dekuNukem/duckyPad/pcb/V2/duckypad v2 dimensions.png

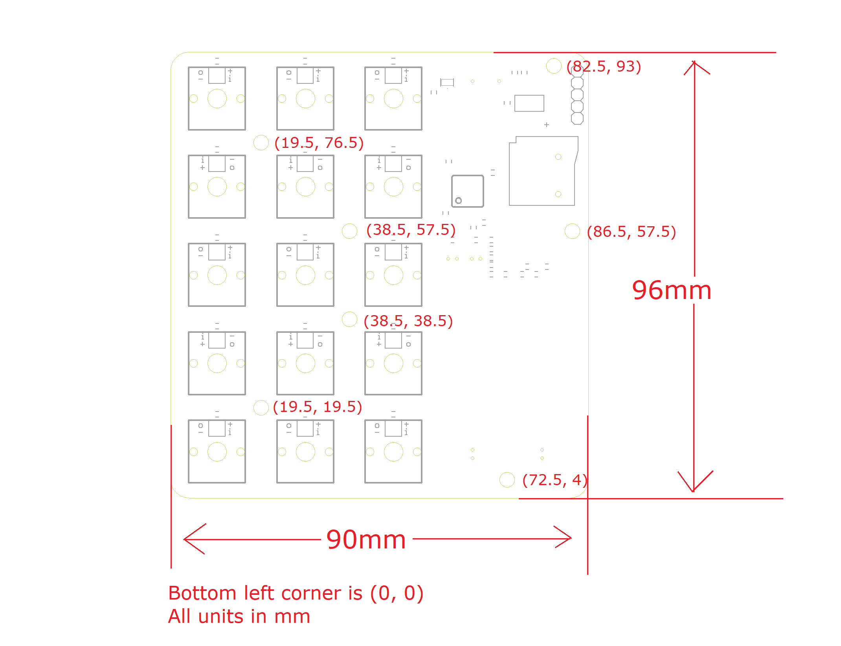
pcb/V2/duckypad v2 dimensions.png
