dekuNukem/duckyPad/resources/Keyboard scancodes Japanese keyboards_files/imb5576-2.jpg

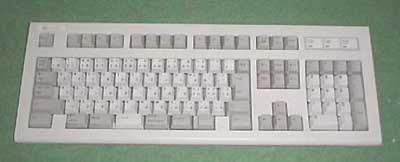
resources/Keyboard scancodes Japanese keyboards_files/imb5576-2.jpg
