dekuNukem/duckyPad/resources/Keyboard scancodes Japanese keyboards_files/jp106-with-scancodes.jpg

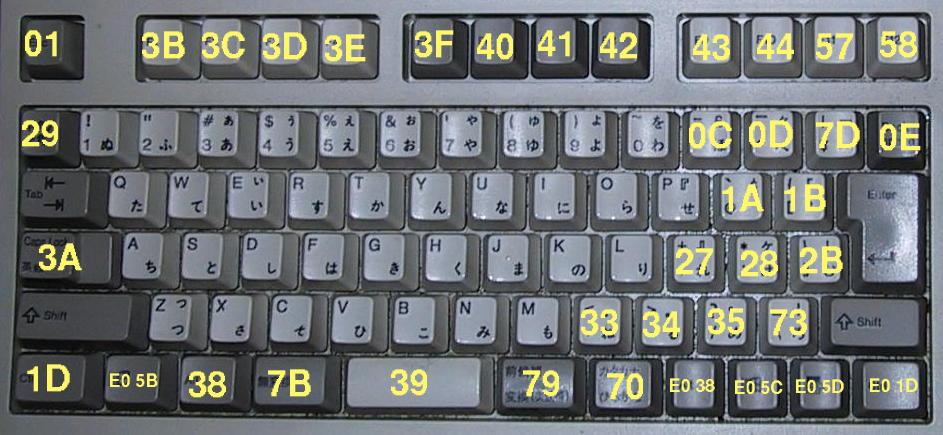
resources/Keyboard scancodes Japanese keyboards_files/jp106-with-scancodes.jpg
