dekuNukem/duckyPad/resources/Keyboard scancodes Japanese keyboards_files/jp106.jpg

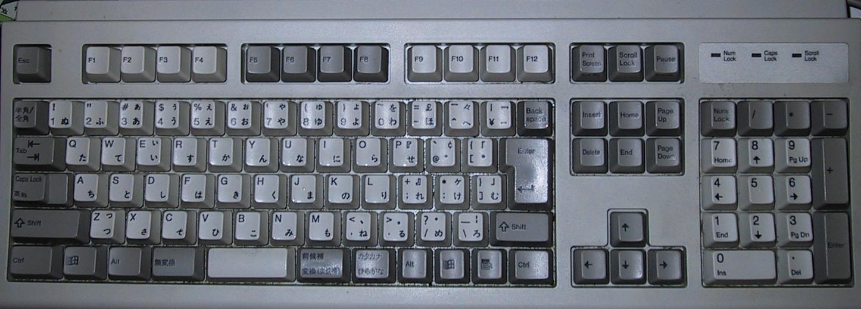
resources/Keyboard scancodes Japanese keyboards_files/jp106.jpg
