dekuNukem/duckyPad/resources/pics/buttons.jpg

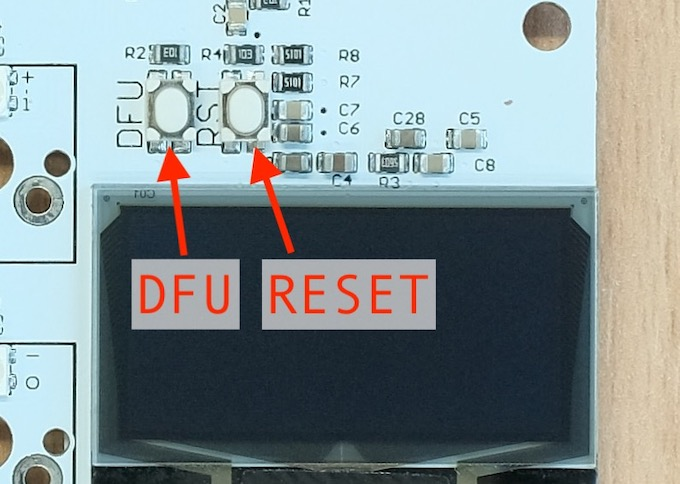
resources/pics/buttons.jpg
