dekuNukem/duckyPad/resources/pics/cable.jpg

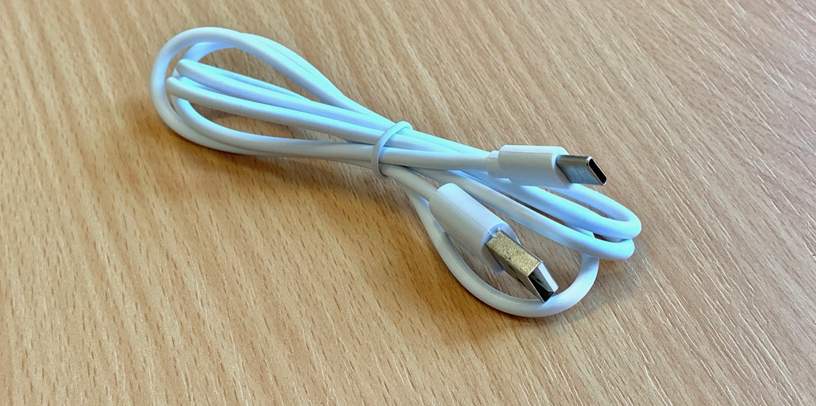
resources/pics/cable.jpg
