dekuNukem/duckyPad/resources/pics/dimensions.png

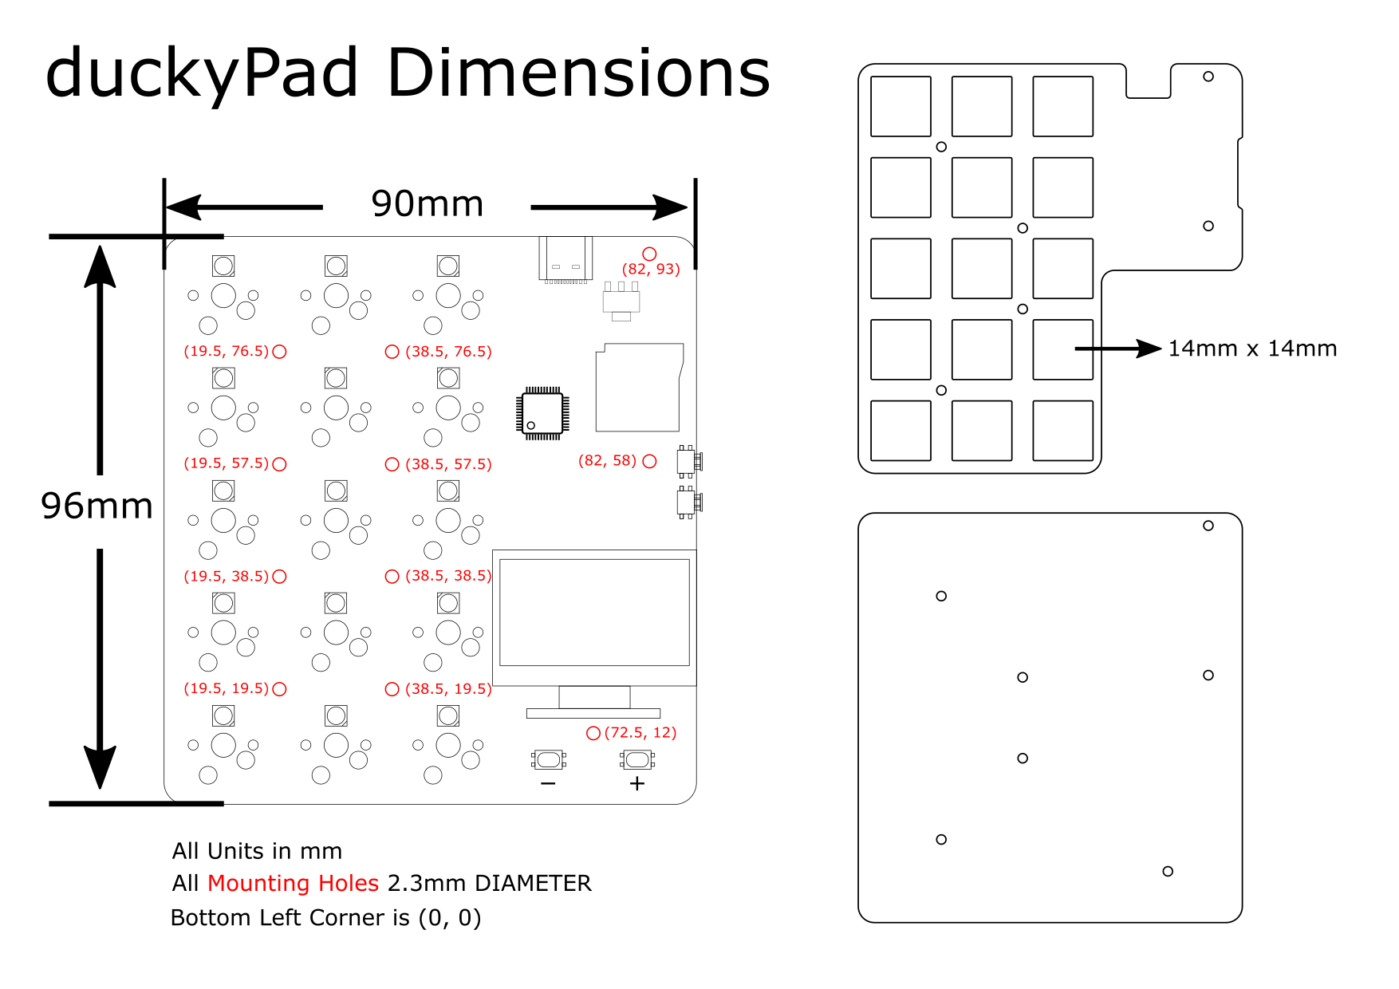
resources/pics/dimensions.png
