dekuNukem/duckyPad/resources/pics/hello.gif

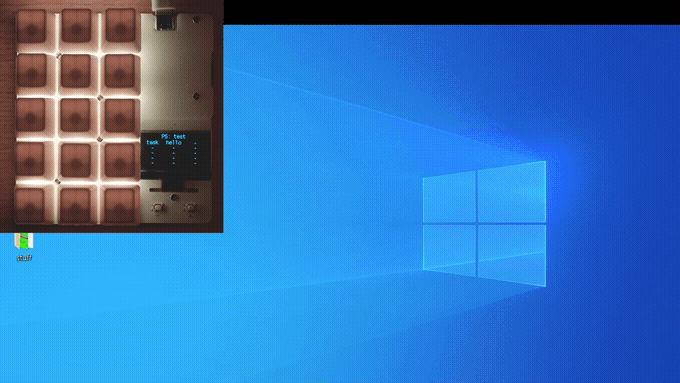
resources/pics/hello.gif
