dekuNukem/duckyPad/resources/pics/input_mon.png

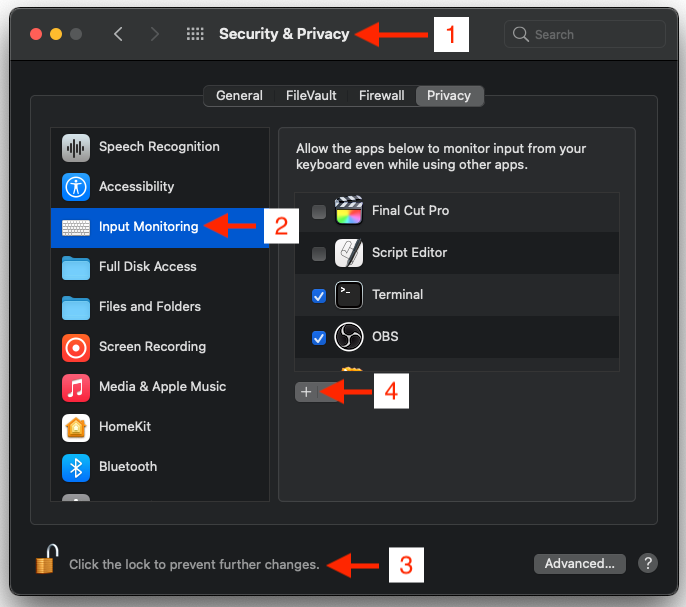
resources/pics/input_mon.png
