dekuNukem/duckyPad/resources/pics/keymaps/dead.png

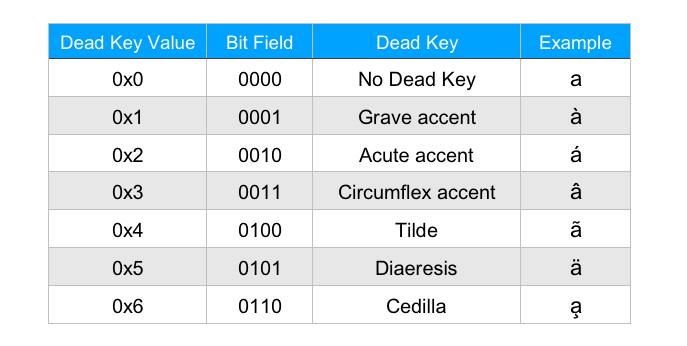
resources/pics/keymaps/dead.png
