dekuNukem/duckyPad/resources/pics/right.png

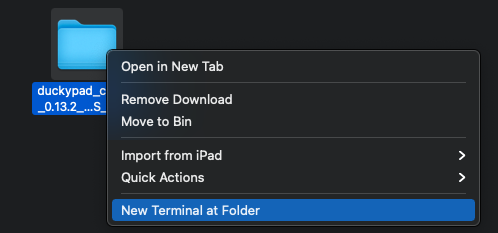
resources/pics/right.png
