dekuNukem/duckyPad/resources/pics/screen_rec.png

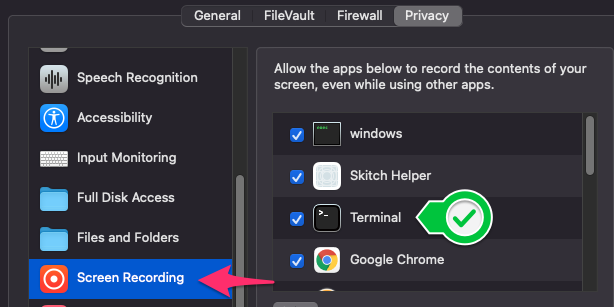
resources/pics/screen_rec.png
