dekuNukem/duckyPad/resources/pics/sd.jpg

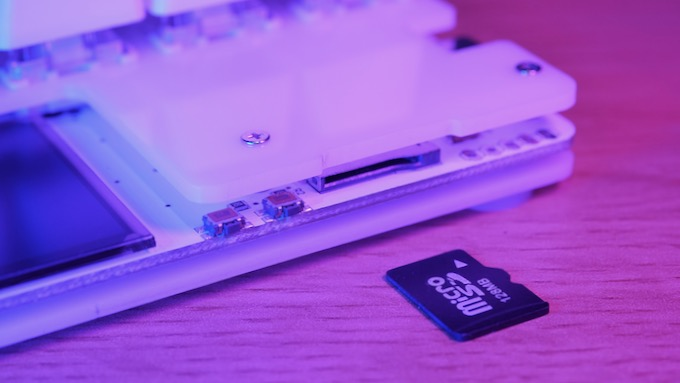
resources/pics/sd.jpg
