dekuNukem/duckyPad/resources/pics/sd_card.PNG

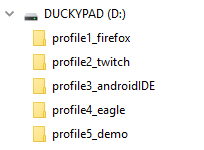
resources/pics/sd_card.PNG
