dekuNukem/duckyPad/resources/pics/sd_reader.jpg

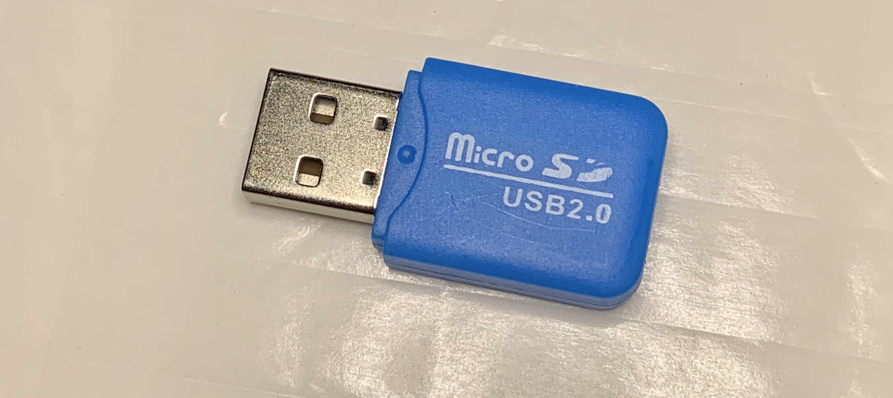
resources/pics/sd_reader.jpg
