dekuNukem/duckyPad/resources/pics/select_term.png

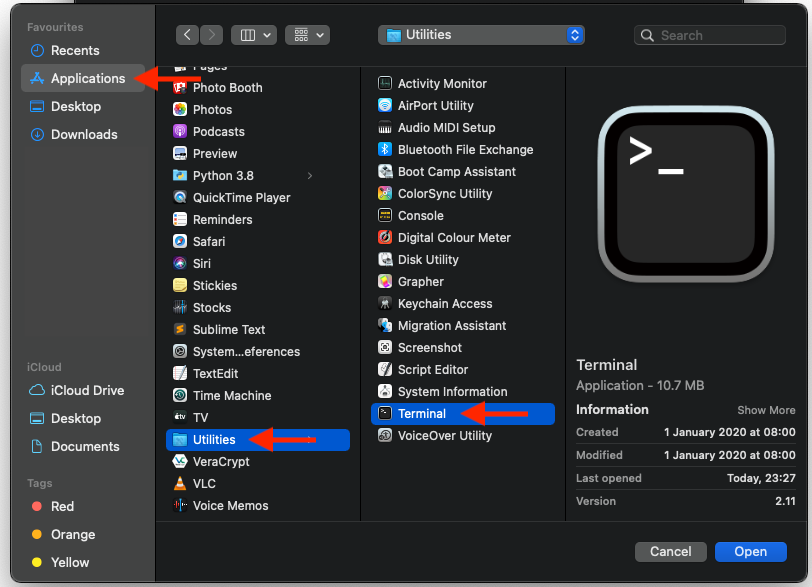
resources/pics/select_term.png
