dekuNukem/duckyPad/resources/pics/start.png

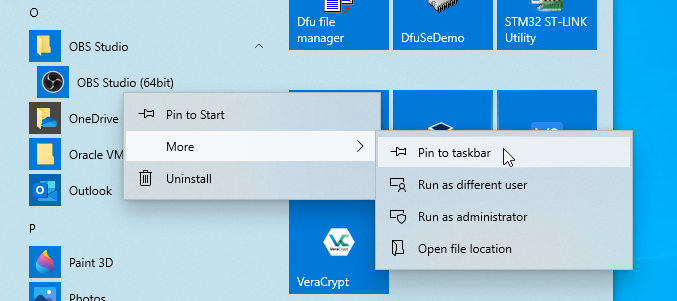
resources/pics/start.png
