dekuNukem/duckyPad/resources/pics/switch.jpg

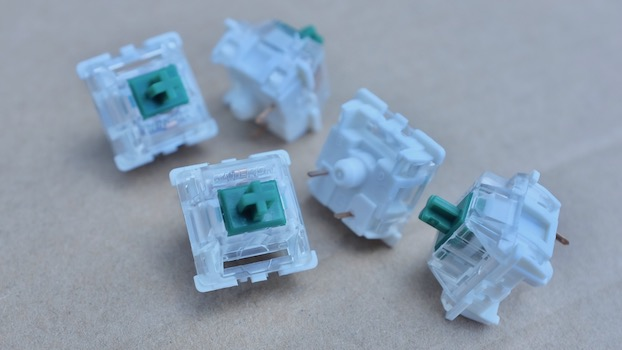
resources/pics/switch.jpg
