dekuNukem/duckyPad/resources/pics/t1.png

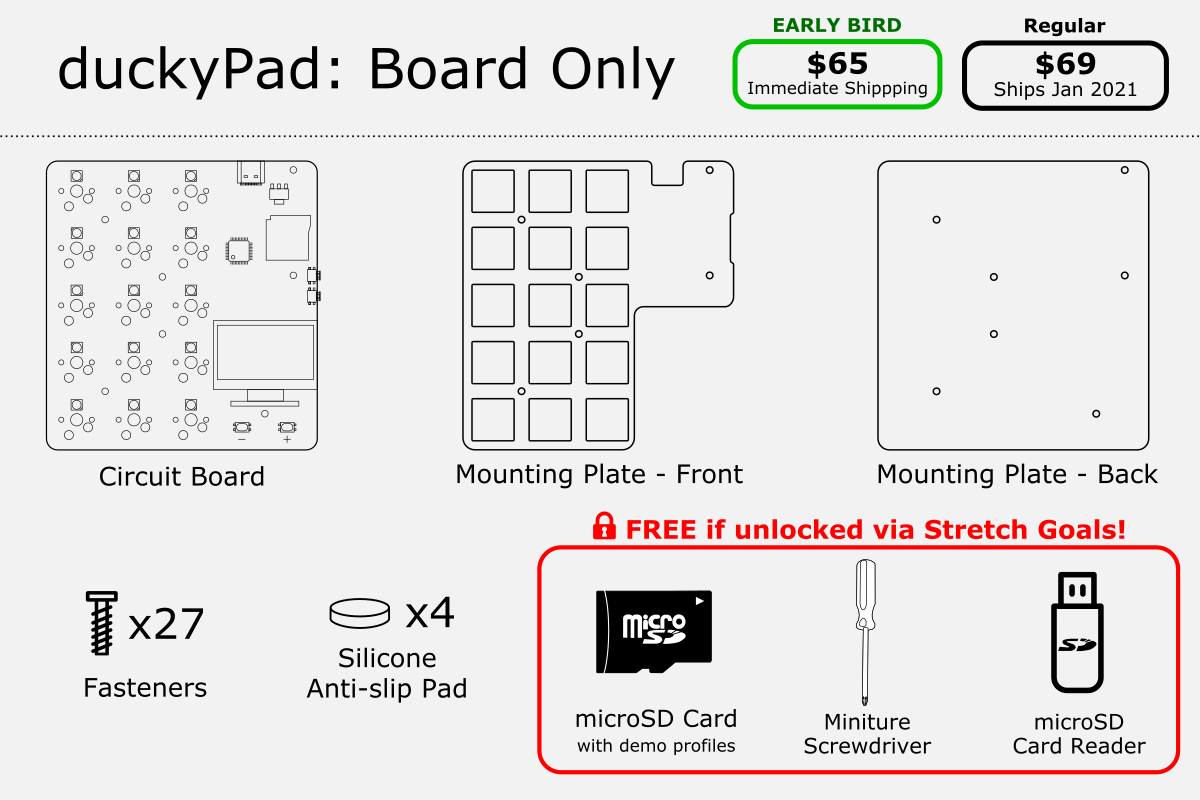
resources/pics/t1.png
