dekuNukem/duckyPad/resources/pics/t2.png

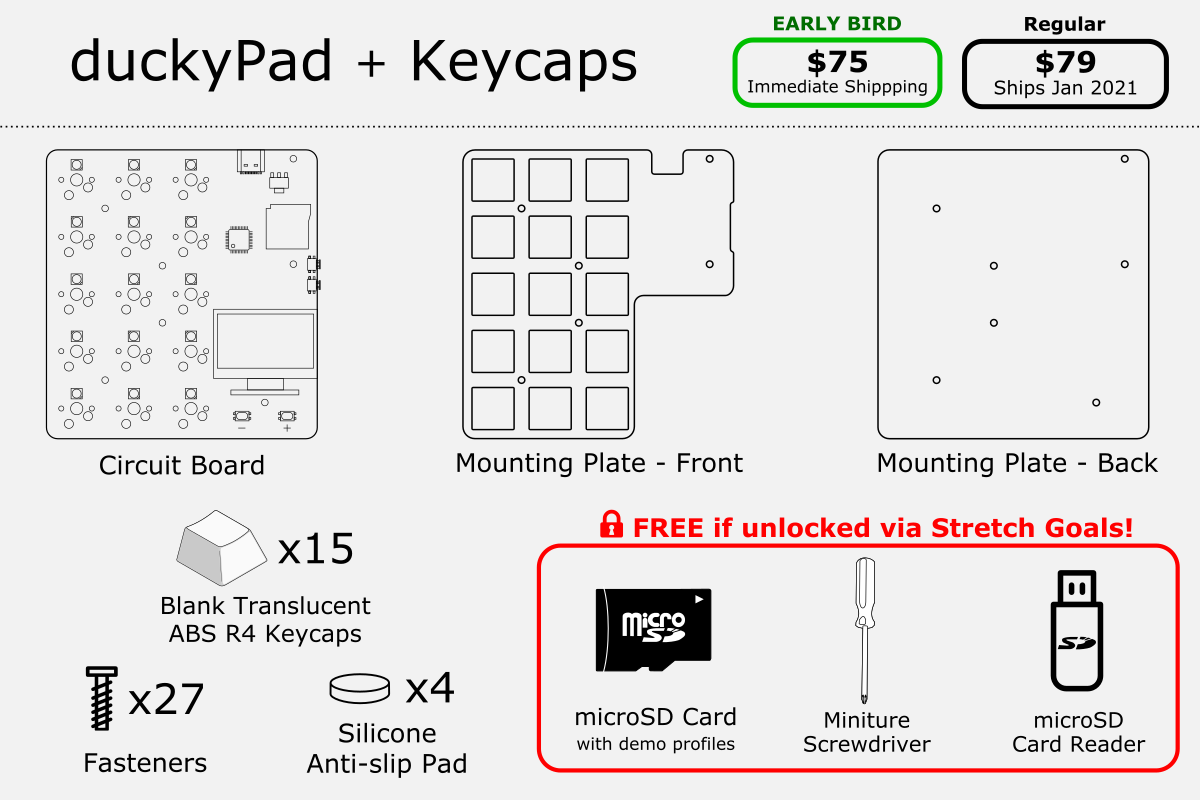
resources/pics/t2.png
