dekuNukem/duckyPad/resources/pics/t3.png

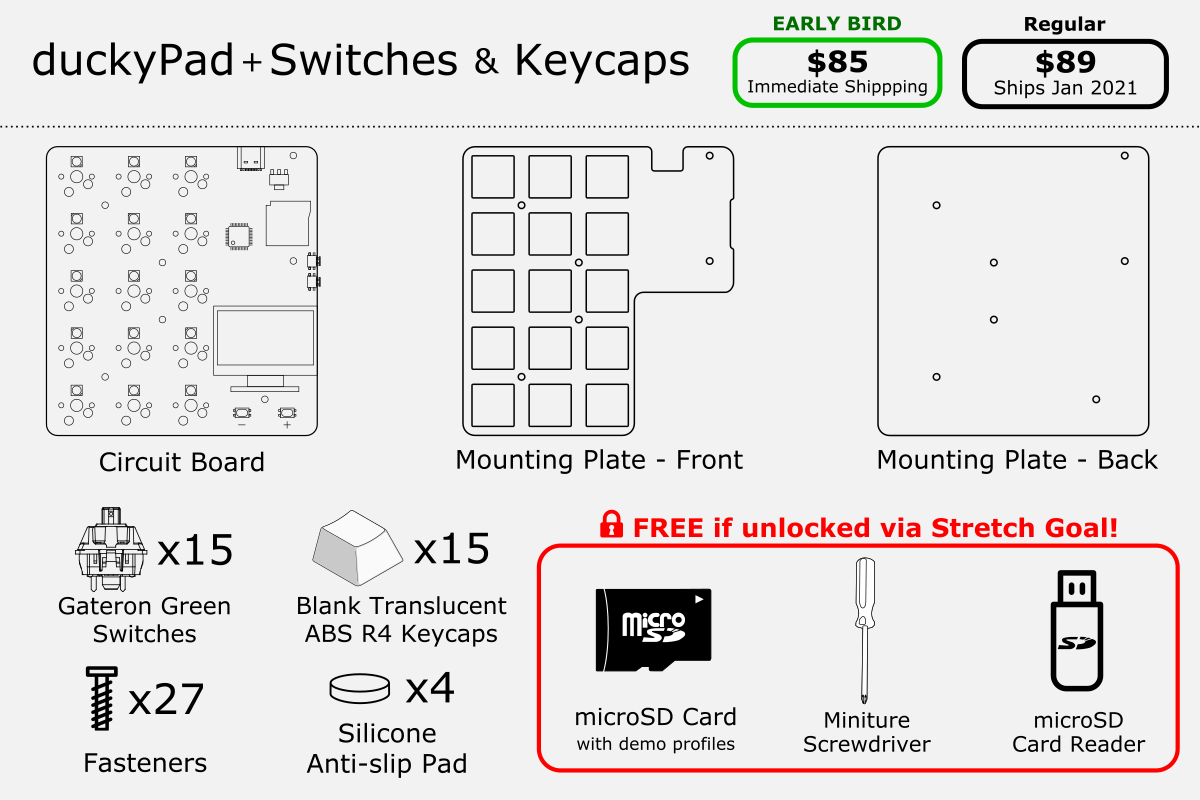
resources/pics/t3.png
