dekuNukem/duckyPad/resources/pics/task.gif

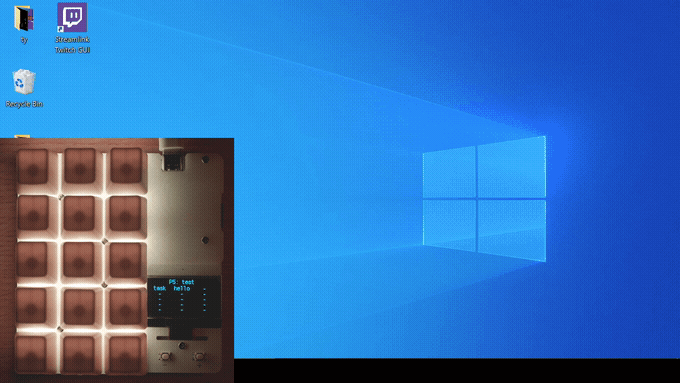
resources/pics/task.gif
