dekuNukem/duckyPad/resources/pics/terminal.png

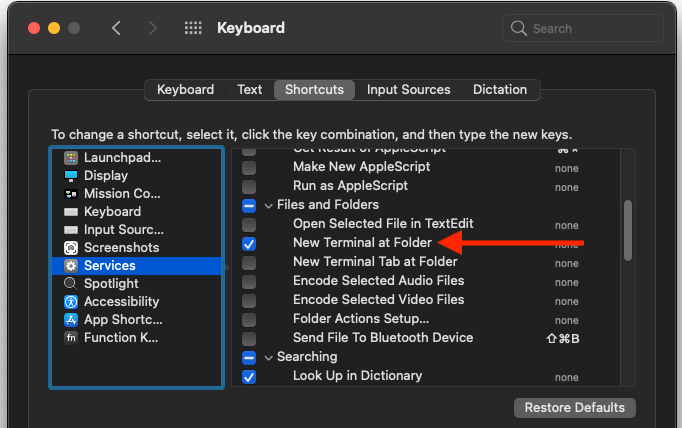
resources/pics/terminal.png
