dekuNukem/duckyPad/resources/pics/tier1.jpg

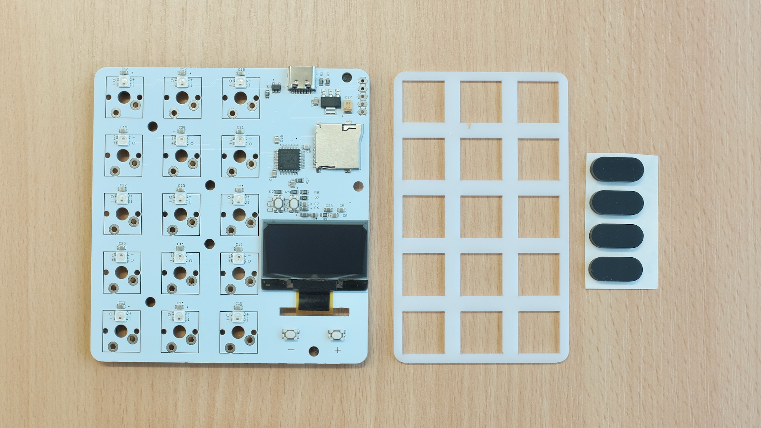
resources/pics/tier1.jpg
