dekuNukem/duckyPad/resources/pics/tier2.jpg

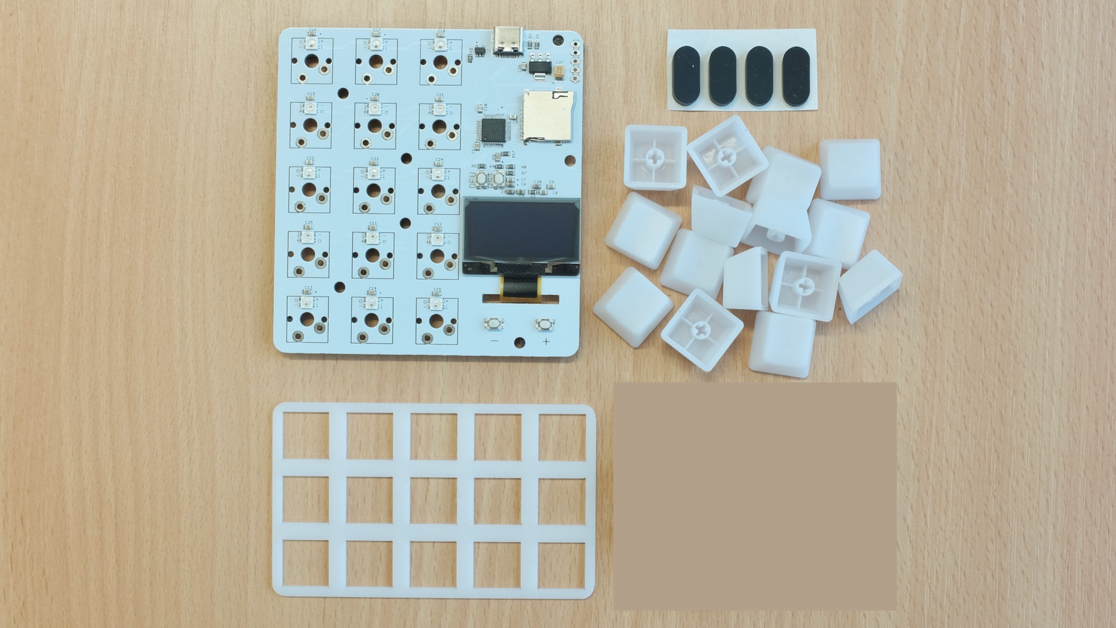
resources/pics/tier2.jpg
