dekuNukem/duckyPad/resources/pics/tier3.jpg

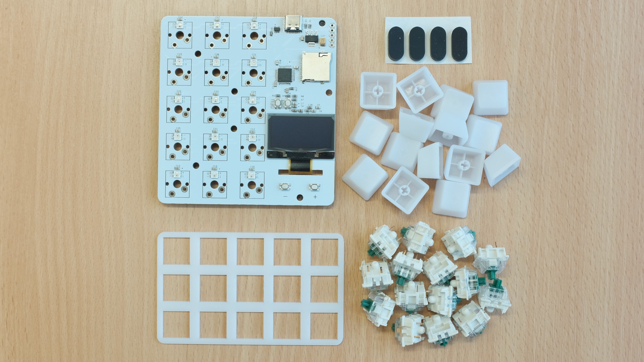
resources/pics/tier3.jpg
