dekuNukem/duckyPad/resources/pics/topdown.jpg

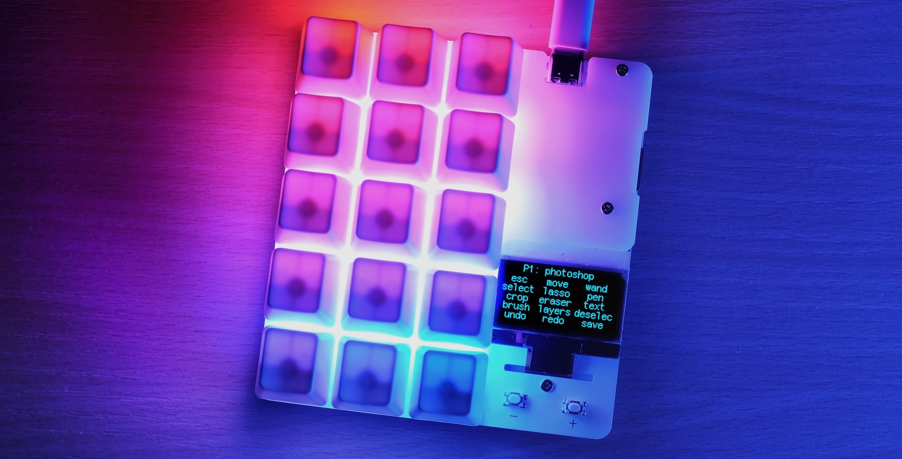
resources/pics/topdown.jpg
