dekuNukem/duckyPad/resources/pics/video.png

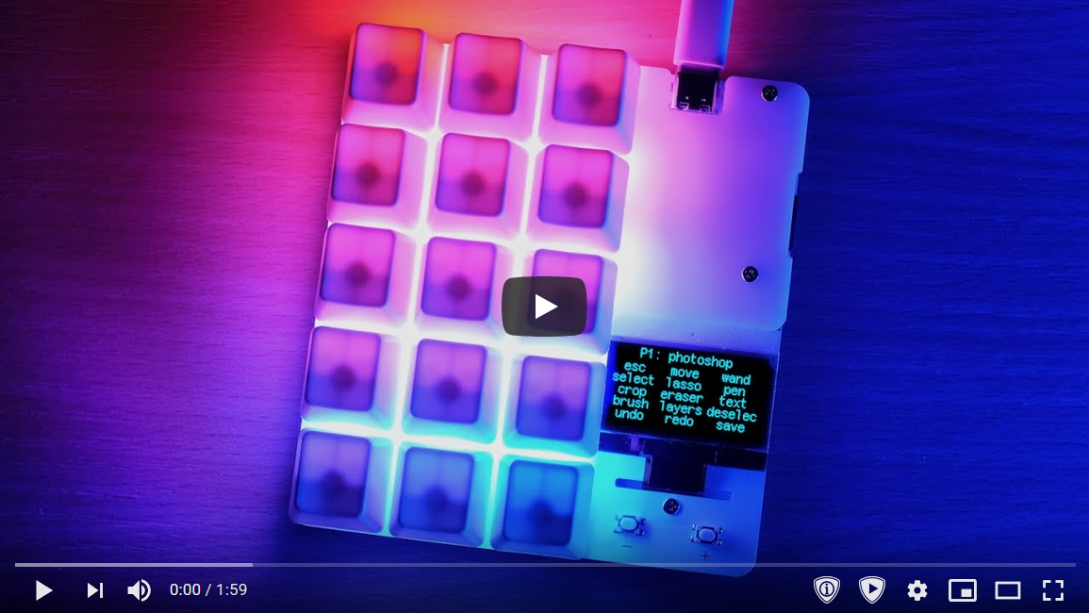
resources/pics/video.png
