dekuNukem/duckyPad/resources/pics/win.png

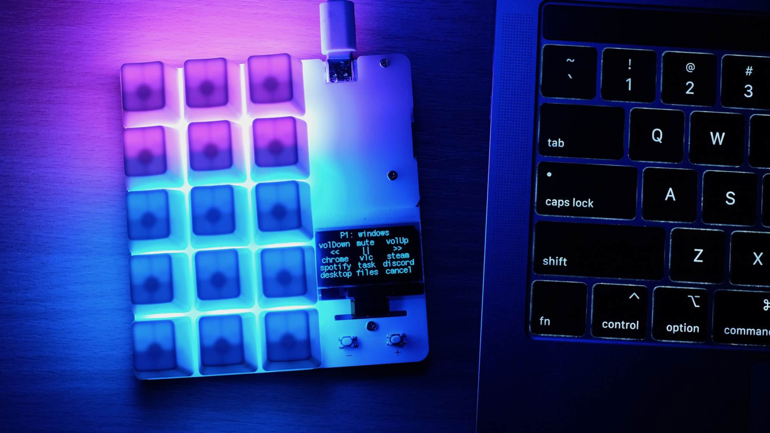
resources/pics/win.png
