dekuNukem/duckyPad/resources/pics/winapps.gif

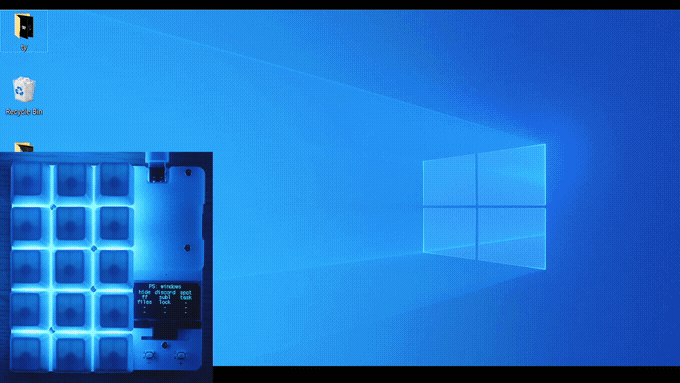
resources/pics/winapps.gif
