dekuNukem/duckyPad/resources/color_tests/image.png

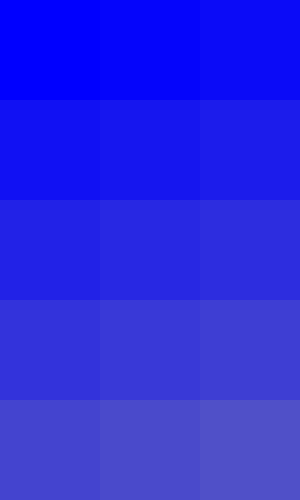
resources/color_tests/image.png
