dekuNukem/duckyPad/resources/SparkFun-Cherry-MX-Switch-Breakout.brd

## EAGLE design resources/SparkFun-Cherry-MX-Switch-Breakout.brd (2019-06-09)

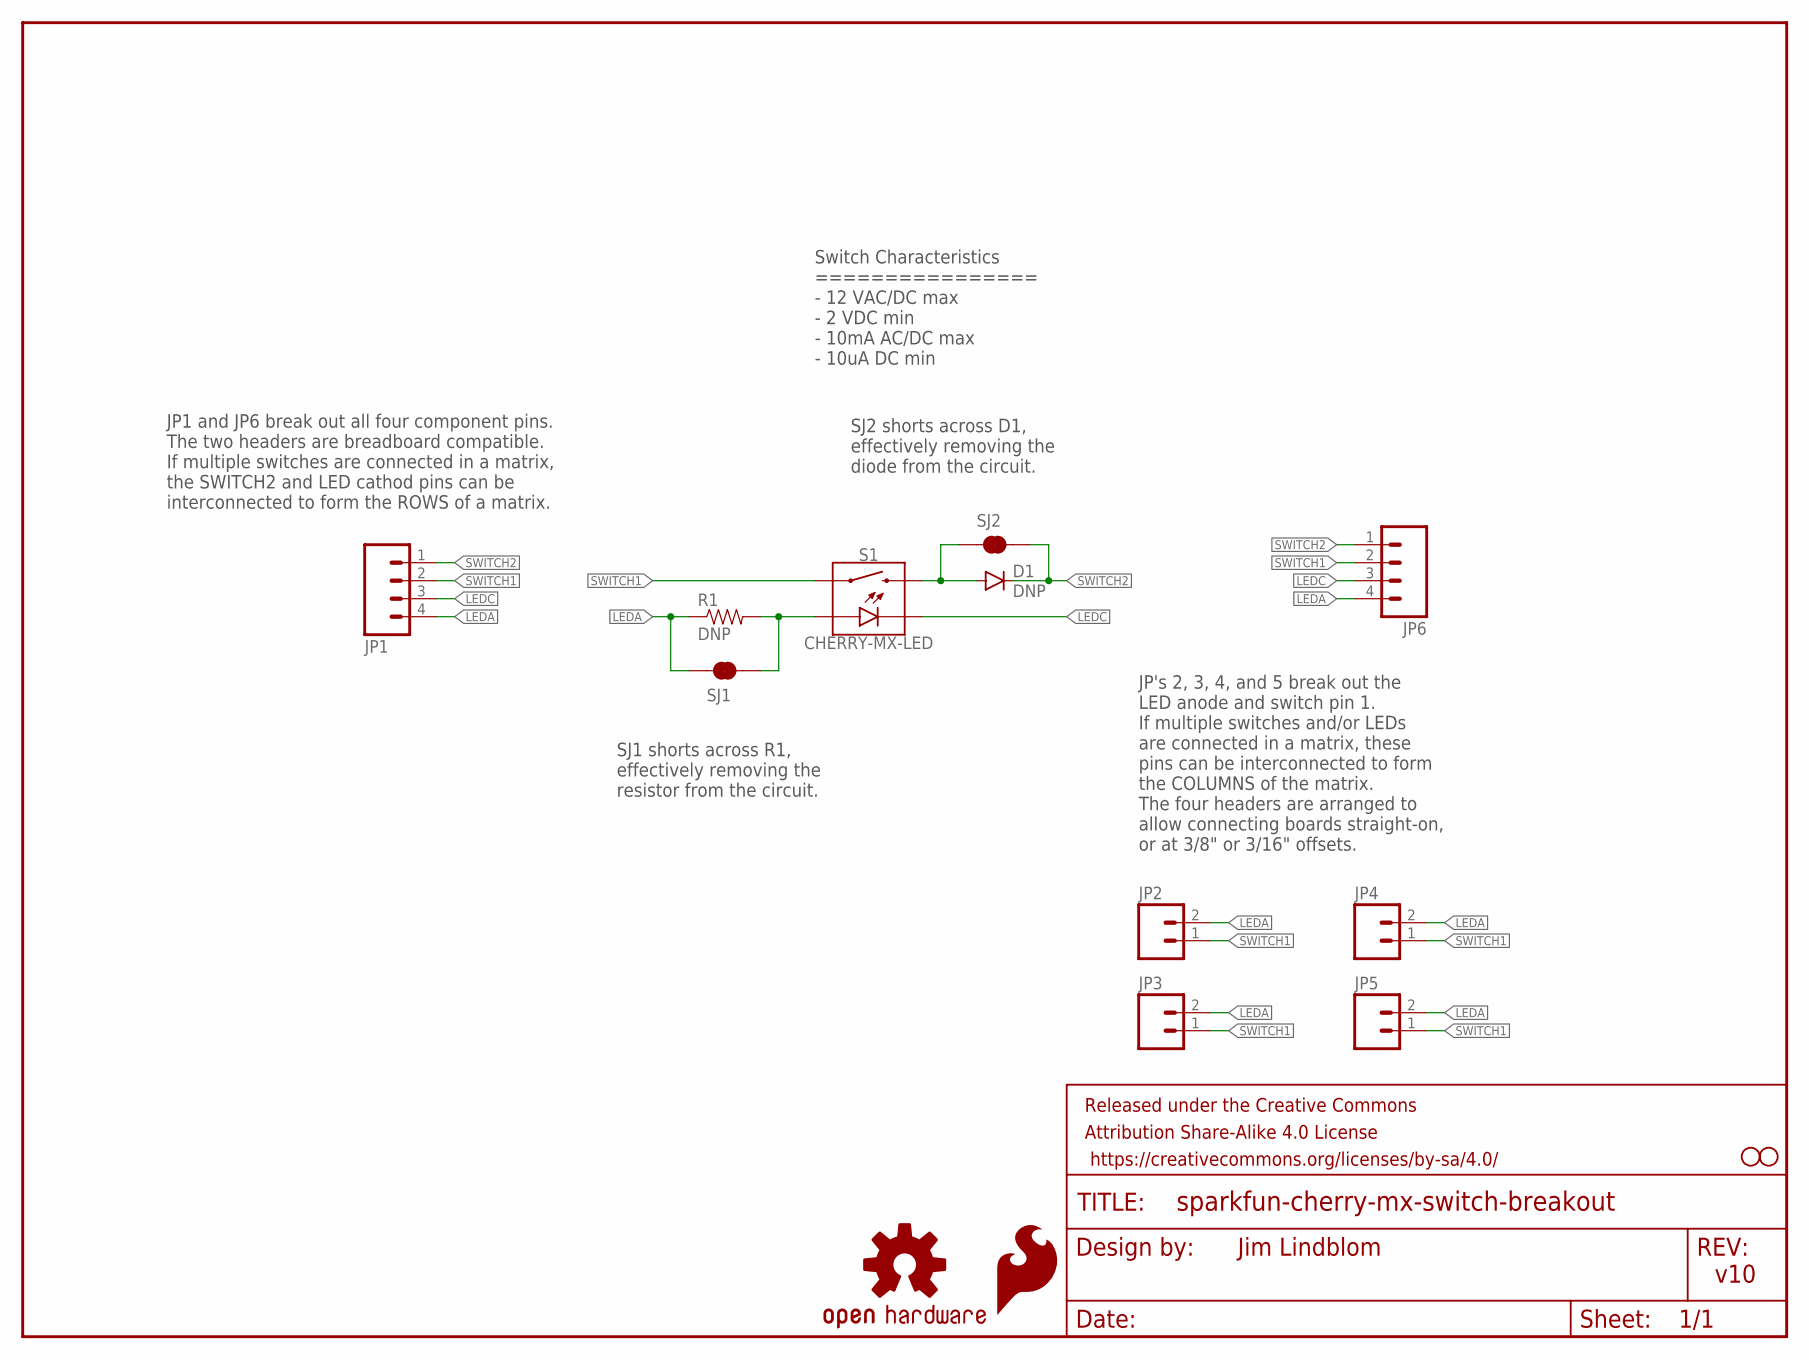
[picture p116: schematic SparkFun-Cherry-MX-Switch-Breakout.sch]

Parts:
D1: DNP; DIODE-PTH-0.1
FRAME1: FRAME-LETTER; CREATIVE_COMMONS
JP1, JP6: M04NO_SILK_ALL_ROUND; 1X04_NO_SILK_ALL_ROUND
JP2, JP3, JP4, JP5: M021X02_NO_SILK; 1X02_NO_SILK
LOGO1: OSHW-LOGOS; OSHW-LOGO-S
LOGO2: SFE_LOGO_FLAME.1_INCH; SFE_LOGO_FLAME_.1
R1: DNP; AXIAL-0.1
S1: CHERRY-MX-LED
SJ1, SJ2: JUMPER-PAD-2-NC_BY_TRACENO_SILK; PAD-JUMPER-2-NC_BY_TRACE_NO_SILK
STANDOFF1, STANDOFF2: STAND-OFF2-56; STAND-OFF-2-56

Connections:
LEDA: JP1.4, JP2.2, JP3.2, JP4.2, JP5.2, JP6.4, R1.P$1 (1), SJ1.1
LEDC: JP1.3, JP6.3, S1.K (C)
unnamed: R1.P$2 (2), S1.A, SJ1.2
unnamed: D1.A, S1.S2, SJ2.1
SWITCH1: JP1.2, JP2.1, JP3.1, JP4.1, JP5.1, JP6.2, S1.S1
SWITCH2: D1.C, JP1.1, JP6.1, SJ2.2

Notes on the sheet:
v10
Jim Lindblom
SJ1 shorts across R1, effectively removing the resistor from the circuit.
SJ2 shorts across D1, effectively removing the diode from the circuit.
JP's 2, 3, 4, and 5 break out the LED anode and switch pin 1. If multiple switches and/or LEDs are connected in a matrix, these pins can be interconnected to form the COLUMNS of the matrix. The four headers are arranged to allow connecting boards straight-on, or at 3/8" or 3/16" offsets.
JP1 and JP6 break out all four component pins. The two headers are breadboard compatible. If multiple switches are connected in a matrix, the SWITCH2 and LED cathod pins can be interconnected to form the ROWS of a matrix.
Switch Characteristics ================ - 12 VAC/DC max - 2 VDC min - 10mA AC/DC max - 10uA DC min

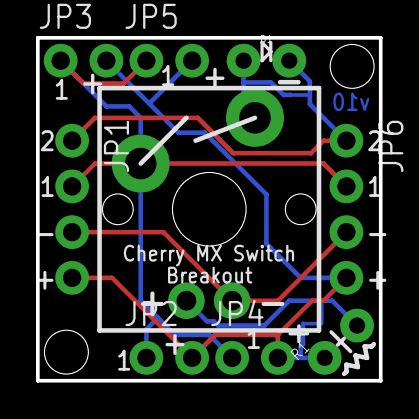
[picture p117: board SparkFun-Cherry-MX-Switch-Breakout.brd from above]

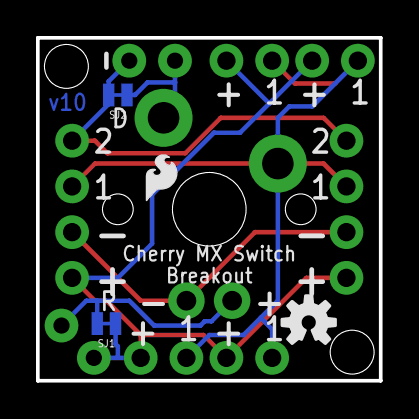
[picture p118: board SparkFun-Cherry-MX-Switch-Breakout.brd from below]

Board: 2 copper layers, 19.1 x 19.1 mm, 16 parts (4 on the bottom side), 6 nets.
