dekuNukem/duckyPad/resources/Adafruit-1.3inch-128x64-Mono-OLED-PCB-master/Adafruit_1.3_128x64_OLED.brd

## EAGLE design resources/Adafruit-1.3inch-128x64-Mono-OLED-PCB-master/Adafruit_1.3_128x64_OLED.brd (2017-08-24)

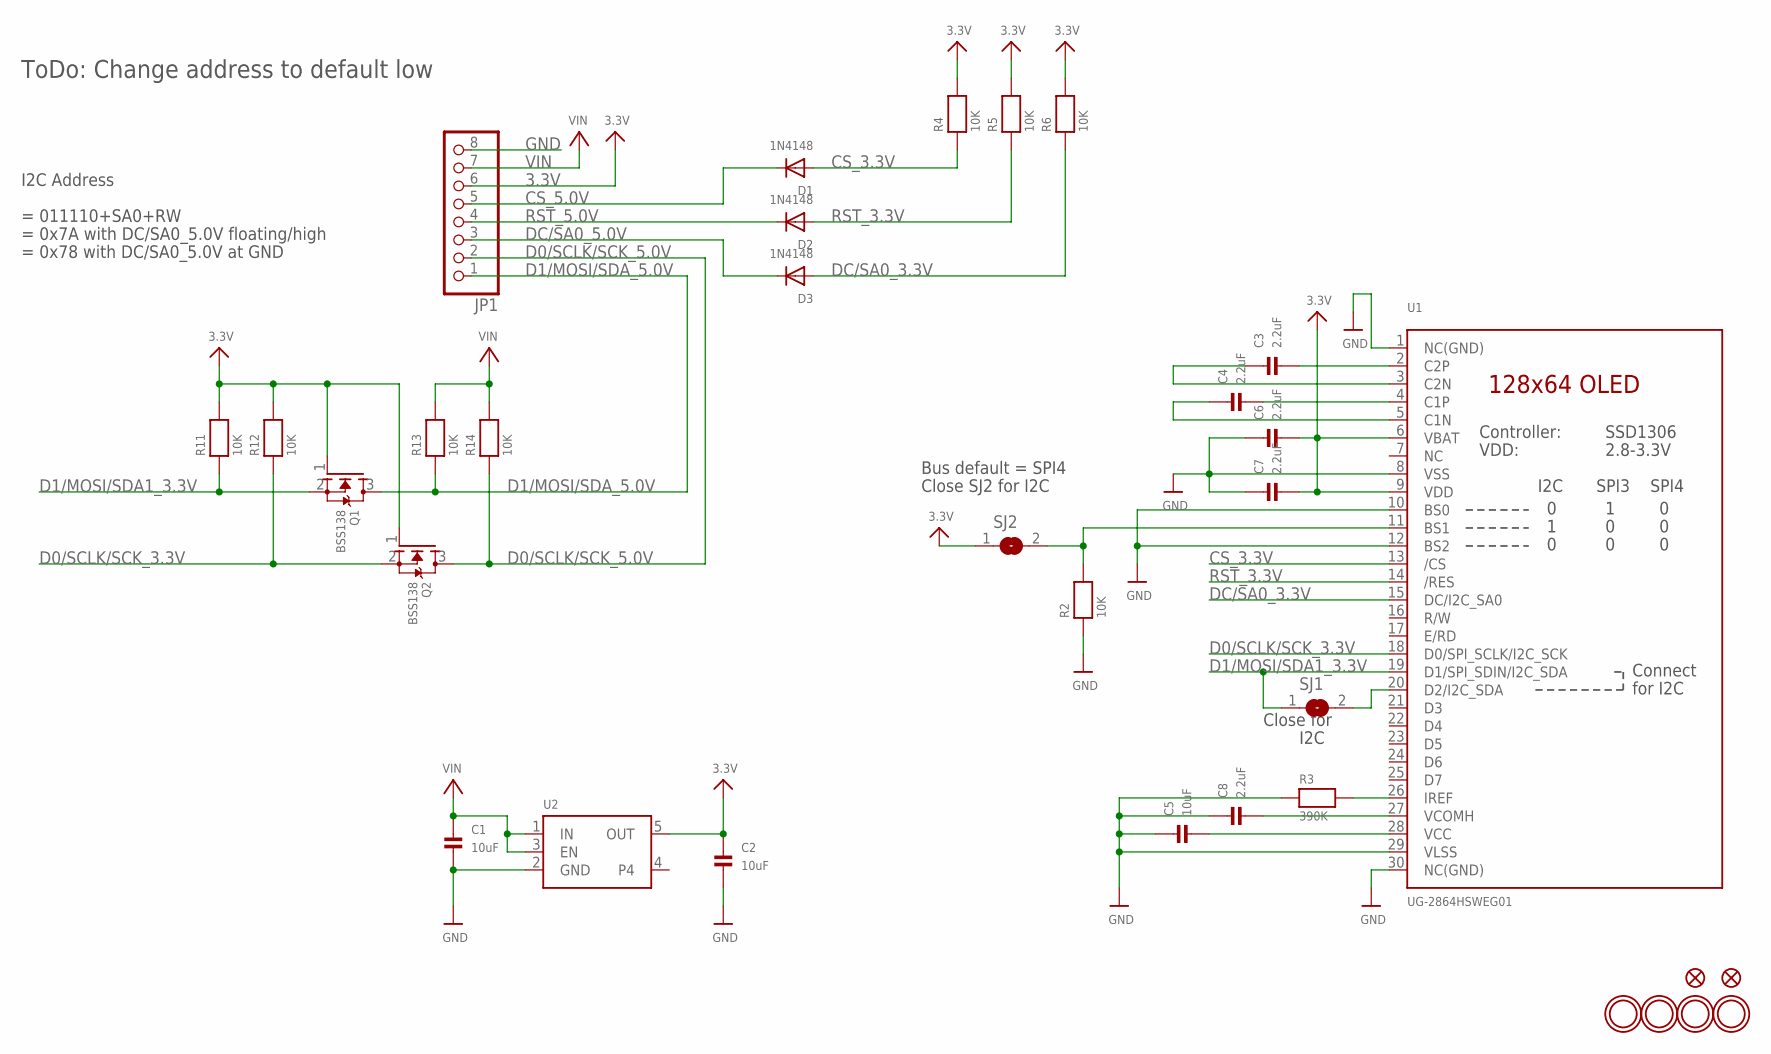
[picture p119: schematic Adafruit_1.3_128x64_OLED.sch]

Parts:
C1, C2, C5: 10uF; 0805
C3, C4, C6, C7, C8: 2.2uF; 0805
D1, D2, D3: 1N4148; SOD-323
FID1, FID2: FIDUCIAL""; FIDUCIAL_1MM
JP1: HEADER-1X870MIL; 1X08_ROUND_70
Q1, Q2: BSS138; SOT23-WIDE
R2, R4, R5, R6, R11, R12, R13, R14: 10K; 0805
R3: 390K; 0805
SJ1, SJ2: SOLDERJUMPERREFLOW_NOPASTE; SOLDERJUMPER_REFLOW_NOPASTE
U1: UG-2864HSWEG01; UG-2864HSWEG01_1.3_WRAPAROUND
U2: VREG_SOT23-5; SOT23-5
U$23, U$24, U$25, U$26: MOUNTINGHOLE2.5; MOUNTINGHOLE_2.5_PLATED

Connections:
3.3V: C2.1, C6.2, C7.2, JP1.6, Q1.1 (G), Q2.1 (G), R4.2, R5.2, R6.2, R11.2, R12.2, SJ2.1, U1.6 (VBAT), U1.9 (VDD), U2.5 (OUT)
CS_3.3V: D1.A, R4.1, U1.13 (/CS)
CS_5.0V: D1.C, JP1.5
D0/SCLK/SCK_3.3V: Q2.2 (S), R12.1, U1.18 (D0/SPI_SCLK/I2C_SCK)
D0/SCLK/SCK_5.0V: JP1.2, Q2.3 (D), R14.1
D1/MOSI/SDA1_3.3V: Q1.2 (S), R11.1, SJ1.1, U1.19 (D1/SPI_SDIN/I2C_SDA)
D1/MOSI/SDA_5.0V: JP1.1, Q1.3 (D), R13.1
DC/SA0_3.3V: D3.A, R6.1, U1.15 (DC/I2C_SA0)
DC/SA0_5.0V: D3.C, JP1.3
GND: C1.2, C2.2, C5.1, C6.1, C7.1, C8.1, JP1.8, R2.1, R3.1, U1.1 (NC(GND)), U1.8 (VSS), U1.10 (BS0), U1.12 (BS2), U1.29 (VLSS), U1.30 (NC(GND)), U2.2 (GND)
unnamed: R2.2, SJ2.2, U1.11 (BS1)
unnamed: SJ1.2, U1.20 (D2/I2C_SDA)
unnamed: R3.2, U1.26 (IREF)
unnamed: C3.2, U1.2 (C2P)
unnamed: C3.1, U1.3 (C2N)
unnamed: C4.2, U1.4 (C1P)
unnamed: C4.1, U1.5 (C1N)
unnamed: C5.2, U1.28 (VCC)
unnamed: C8.2, U1.27 (VCOMH)
RST_3.3V: D2.A, R5.1, U1.14 (/RES)
RST_5.0V: D2.C, JP1.4
VIN: C1.1, JP1.7, R13.2, R14.2, U2.1 (IN), U2.3 (EN)

Notes on the sheet:
Bus default = SPI4
Close SJ2 for I2C
= 011110+SA0+RW
= 0x7A with DC/SA0_5.0V floating/high
= 0x78 with DC/SA0_5.0V at GND
I2C Address
ToDo: Change address to default low
Close for
I2C

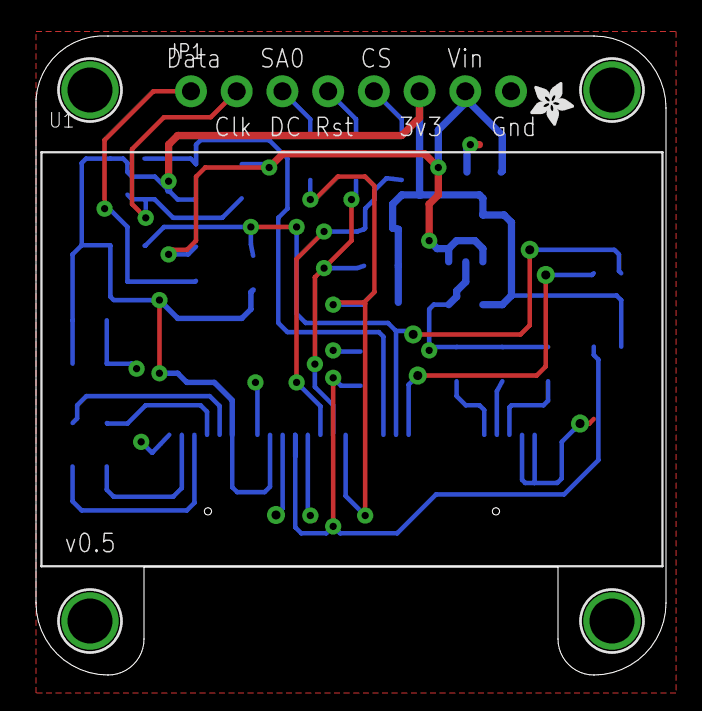
[picture p120: board Adafruit_1.3_128x64_OLED.brd from above]

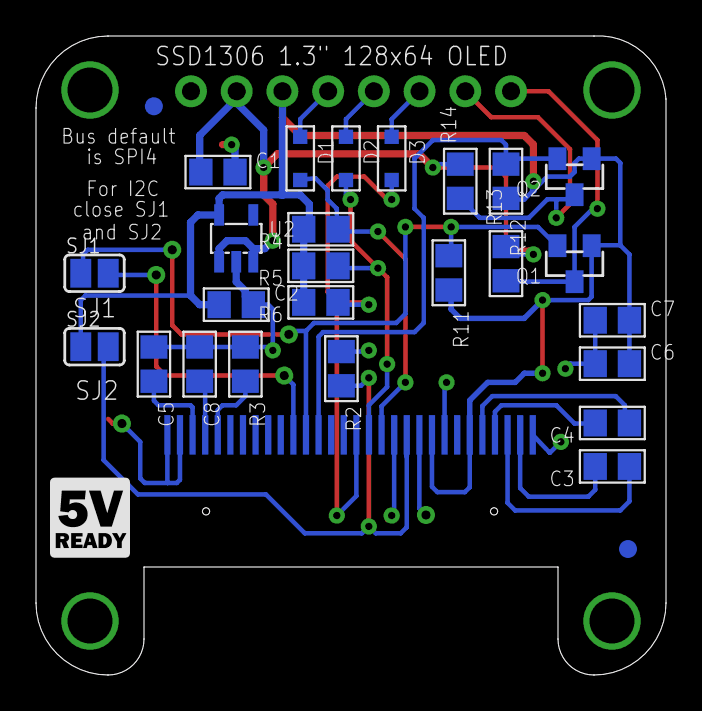
[picture p121: board Adafruit_1.3_128x64_OLED.brd from below]

Board: 2 copper layers, 35.0 x 35.5 mm, 35 parts (28 on the bottom side), 22 nets.

Other parts of the board:
U$27: ADAFRUIT_2.5MM
U$28: LOGIC_5VREADY_5MM
