dekuNukem/duckyPad/firmware/code/Src/main.c

/**
  ******************************************************************************
  * @file           : main.c
  * @brief          : Main program body
  ******************************************************************************
  * This notice applies to any and all portions of this file
  * that are not between comment pairs USER CODE BEGIN and
  * USER CODE END. Other portions of this file, whether 
  * inserted by the user or by software development tools
  * are owned by their respective copyright owners.
  *
  * Copyright (c) 2021 STMicroelectronics International N.V. 
  * All rights reserved.
  *
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
  ******************************************************************************
  */
/* Includes ------------------------------------------------------------------*/
#include "main.h"
#include "stm32f0xx_hal.h"
#include "cmsis_os.h"
#include "fatfs.h"
#include "usb_device.h"

/* USER CODE BEGIN Includes */
#include <stdio.h>
#include <string.h>
#include <stdlib.h>
#include "usbd_customhid.h"
#include "ssd1306.h"
#include "fonts.h"
#include "neopixel.h"
#include "buttons.h"
#include "keyboard.h"
#include "parser.h"
#include "shared.h"
#include "my_tasks.h"
#include "animations.h"

/* USER CODE END Includes */

I2C_HandleTypeDef hi2c1;

IWDG_HandleTypeDef hiwdg;

SPI_HandleTypeDef hspi1;

UART_HandleTypeDef huart1;

osThreadId kb_scanHandle;

/* USER CODE BEGIN PV */

/*
0.20.3 20221031
changed HOLD to EMUK

0.20.4 20221114
add JIS keys

0.21.0 20221117
changed USB HID descriptor so new japanese keys work

0.21.1 20221221
cleaned up animation code
tried out no animation at all, frees up about 1K of ram

0.21.2
massive overhaul to reduce RAM and ROM usage
using hashed lookup for string matching
new keymap select screen
reduced RTOS heap usage
cleaned up animation, much faster
no functional changes
mouse button not implemented yet

0.22.0 20230111
added mouse commands back
ready for public release

0.22.1 20230118
fixed a bug where STRING prints an extra space

1.0.0 20230202
beta release for duckyscript 3

1.1.0 20230214
added banked loading for large dsb files
cleaned up opcode values

1.1.1 20230215
fixed a bug where screen doesnt update when exiting keymap selection screen

1.1.2 20230221
added busy state

1.1.3 20230329
fixing a rand() bug where modulus power of 2 result in repeating patterns

1.1.4 20230409
fixed a SD card timing bug

1.2.0 20230502
ready for public release

1.2.1 20230630
fixed laggy EMUK
fixed EMUK-related n-key rollover bug
fixed pad crashing when changing profiles

1.3.0 20230701
added _TIME_S read-only variable

1.3.1
20231111
increased max profiles to 64
change MAX_PROFILES in parser.h
change BIN_BUF_SIZE in ds3_vm.c if out of space

1.3.2
2024 01 22
fixed backlight brightness saving bug

1.3.3
2024 12 02
Fixed non-responsive mouse scroll bug 

1.3.4
2024 12 18
Fixed dead key behaviour
*/

uint8_t fw_version_major = 1;
uint8_t fw_version_minor = 3;
uint8_t fw_version_patch = 4;
char instruction[] = "For instructions, see";
/* USER CODE END PV */

void SystemClock_Config(void);
static void MX_GPIO_Init(void);
static void MX_USART1_UART_Init(void);
static void MX_SPI1_Init(void);
static void MX_I2C1_Init(void);
static void MX_IWDG_Init(void);
void kb_scan_task(void const * argument);
/* USER CODE BEGIN PFP */

/* USER CODE END PFP */

/* USER CODE BEGIN 0 */
int fputc(int ch, FILE *f)
{
    HAL_UART_Transmit(&huart1, (unsigned char *)&ch, 1, 100);
    return ch;
}
/* USER CODE END 0 */

/**
  * @brief  The application entry point.
  *
  * @retval None
  */
int main(void)
{
  /* MCU Configuration----------------------------------------------------------*/

  /* Reset of all peripherals, Initializes the Flash interface and the Systick. */
  HAL_Init();

  /* Configure the system clock */
  SystemClock_Config();

  /* Initialize all configured peripherals */
  MX_GPIO_Init();
  MX_USART1_UART_Init();
  MX_SPI1_Init();
  MX_I2C1_Init();
  MX_IWDG_Init();
  /* USER CODE BEGIN RTOS_MUTEX */
  /* add mutexes, ... */
  /* USER CODE END RTOS_MUTEX */

  /* USER CODE BEGIN RTOS_SEMAPHORES */
  /* add semaphores, ... */
  /* USER CODE END RTOS_SEMAPHORES */

  /* USER CODE BEGIN RTOS_TIMERS */
  /* start timers, add new ones, ... */
  /* USER CODE END RTOS_TIMERS */

  /* Create the thread(s) */
  /* definition and creation of kb_scan */
  osThreadDef(kb_scan, kb_scan_task, osPriorityNormal, 0, 256);
  kb_scanHandle = osThreadCreate(osThread(kb_scan), NULL);

  /* USER CODE BEGIN RTOS_THREADS */
  /* add threads, ... */
  // kb_scan_task should have 256 byte
  osThreadDef(keypress_task, keypress_task_start, osPriorityAboveNormal, 0, 512);
  osThreadCreate(osThread(keypress_task), NULL);
  /* USER CODE END RTOS_THREADS */

  /* USER CODE BEGIN RTOS_QUEUES */
  /* add queues, ... */
  /* USER CODE END RTOS_QUEUES */
 

  /* Start scheduler */
  osKernelStart();
  
  /* We should never get here as control is now taken by the scheduler */

  /* Infinite loop */
  /* USER CODE BEGIN WHILE */
  
  while (1)
  {
  /* USER CODE END WHILE */

  /* USER CODE BEGIN 3 */
  }
  /* USER CODE END 3 */

}

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
/* USER CODE BEGIN 4 */
void HAL_GPIO_EXTI_Callback(uint16_t GPIO_Pin)
{
  HAL_Delay(200);
  NVIC_SystemReset();
}

/* USER CODE END 4 */

/* USER CODE BEGIN Header_kb_scan_task */
/**
  * @brief  Function implementing the kb_scan thread.
  * @param  argument: Not used 
  * @retval None
  */
/* USER CODE END Header_kb_scan_task */
void kb_scan_task(void const * argument)
{
  /* init code for FATFS */
  MX_FATFS_Init();

  /* init code for USB_DEVICE */
  MX_USB_DEVICE_Init();

  /* USER CODE BEGIN 5 */
  neopixel_off();
  uint8_t mount_result = f_mount(&sd_fs, "", 1);
  HAL_GPIO_WritePin(OLED_RESET_GPIO_Port, OLED_RESET_Pin, GPIO_PIN_RESET);
  osDelay(10);
  HAL_GPIO_WritePin(OLED_RESET_GPIO_Port, OLED_RESET_Pin, GPIO_PIN_SET);
  osDelay(20);
  ssd1306_Init();
  ssd1306_Fill(Black);
 
  if(mount_result)
  {
    ssd1306_Fill(Black);
    ssd1306_SetCursor(0, 5);
    ssd1306_WriteString("Please Insert SD Card",Font_6x10,White);

    memset(temp_buf, 0, PATH_SIZE);
    sprintf(temp_buf, "FW V%d.%d.%d", fw_version_major, fw_version_minor, fw_version_patch);
    ssd1306_SetCursor(35, 52);
    ssd1306_WriteString(temp_buf,Font_6x10,White);

    ssd1306_SetCursor(0, 22);
    ssd1306_WriteString(instruction,Font_6x10,White);
    ssd1306_SetCursor(24, 35);
    ssd1306_WriteString(project_url,Font_6x10,White);
    ssd1306_UpdateScreen();
    while(1)
    {
      HAL_IWDG_Refresh(&hiwdg);
      osDelay(30);
    }
  }

  load_settings();
  scan_profiles();
  // this line must be after scan_profiles()
  uint8_t last_profile = get_last_profile();
  if(last_profile == 0)
    change_profile(NEXT_PROFILE);
  else
    restore_profile(last_profile);
  
  init_complete = 1;
  /* Infinite loop */
  printf("fhs: %u\n", xPortGetFreeHeapSize());
  anime_init();
  for(;;)
  {
    HAL_IWDG_Refresh(&hiwdg);
    keyboard_update();
    animation_task_start();
    osDelay(16);
  }
  /* USER CODE END 5 */ 
}

/**
  * @brief  Period elapsed callback in non blocking mode
  * @note   This function is called  when TIM6 interrupt took place, inside
  * HAL_TIM_IRQHandler(). It makes a direct call to HAL_IncTick() to increment
  * a global variable "uwTick" used as application time base.
  * @param  htim : TIM handle
  * @retval None
  */
void HAL_TIM_PeriodElapsedCallback(TIM_HandleTypeDef *htim)
{
  if (htim->Instance == TIM6) {
    HAL_IncTick();
  }
}

/**
  * @brief  This function is executed in case of error occurrence.
  * @param  file: The file name as string.
  * @param  line: The line in file as a number.
  * @retval None
  */
void _Error_Handler(char *file, int line)
{
  /* USER CODE BEGIN Error_Handler_Debug */
  /* User can add his own implementation to report the HAL error return state */
  while(1) 
  {
  }
  /* USER CODE END Error_Handler_Debug */
}

#ifdef  USE_FULL_ASSERT
/**
  * @brief  Reports the name of the source file and the source line number
  *         where the assert_param error has occurred.
  * @param  file: pointer to the source file name
  * @param  line: assert_param error line source number
  * @retval None
  */
void assert_failed(uint8_t* file, uint32_t line)
{ 
  /* USER CODE BEGIN 6 */
  /* User can add his own implementation to report the file name and line number,
    ex: printf("Wrong parameters value: file %s on line %d\r\n", file, line) */
  /* USER CODE END 6 */
}
#endif /* USE_FULL_ASSERT */

/**
  * @}
  */

/**
  * @}
  */

/************************ (C) COPYRIGHT STMicroelectronics *****END OF FILE****/
