dekuNukem/duckyPad/firmware/code/Src/ds3_vm.c

#include <stdio.h>    /* printf */
#include <stdint.h>
#include <string.h>
#include <stdlib.h>
#include "ds3_vm.h"
#include "parser.h"
#include "keyboard.h"
#include "animations.h"
#include "ssd1306.h"
#include "buttons.h"
#include "neopixel.h"

// 2300 seems to be max, 2048 just to be safe
#define BIN_BUF_SIZE 2048
uint8_t bin_buf[BIN_BUF_SIZE];
#define VAR_BUF_SIZE 128
uint8_t var_buf[VAR_BUF_SIZE];
uint8_t current_bank;
uint16_t defaultdelay_value;
uint16_t defaultchardelay_value;
uint16_t charjitter_value;
uint32_t rand_min, rand_max;
uint16_t loop_size;
uint8_t epilogue_actions;

typedef struct
{
  uint8_t top;
  uint16_t stack[STACK_SIZE];
} my_stack;

my_stack arithmetic_stack, call_stack;

void stack_init(my_stack* ms)
{
  ms->top = 0;
  memset(ms->stack, 0, STACK_SIZE);
}

uint8_t stack_push(my_stack* ms, uint16_t value)
{
  if(ms->top >= STACK_SIZE)
    return STACK_OP_OVERFLOW;
  ms->stack[ms->top] = value;
  ms->top++;
  return STACK_OP_OK;
}

uint8_t stack_pop(my_stack* ms, uint16_t *result)
{
  if(ms->top == 0)
    return STACK_OP_UNDERFLOW;
  ms->top--;
  *result = ms->stack[ms->top];
  ms->stack[ms->top] = 0;
  return STACK_OP_OK;
}

uint16_t make_uint16(uint8_t b0, uint8_t b1)
{
  return b0 | (b1 << 8);
}

uint16_t binop_add(uint16_t a, uint16_t b) {return a + b;}
uint16_t binop_sub(uint16_t a, uint16_t b) {return a - b;}
uint16_t binop_mul(uint16_t a, uint16_t b) {return a * b;}
uint16_t binop_divide(uint16_t a, uint16_t b) {return a / b;}
uint16_t binop_mod(uint16_t a, uint16_t b) {return a % b;}
uint16_t binop_greater(uint16_t a, uint16_t b) {return a > b;}
uint16_t binop_greater_eq(uint16_t a, uint16_t b) {return a >= b;}
uint16_t binop_lower(uint16_t a, uint16_t b) {return a < b;}
uint16_t binop_lower_eq(uint16_t a, uint16_t b) {return a <= b;}
uint16_t binop_equal(uint16_t a, uint16_t b) {return a == b;}
uint16_t binop_not_equal(uint16_t a, uint16_t b) {return a != b;}
uint16_t binop_bitwise_and(uint16_t a, uint16_t b) {return a & b;}
uint16_t binop_bitwise_or(uint16_t a, uint16_t b) {return a | b;}
uint16_t binop_lshift(uint16_t a, uint16_t b) {return a << b;}
uint16_t binop_rshift(uint16_t a, uint16_t b) {return a >> b;}
uint16_t binop_logical_and(uint16_t a, uint16_t b) {return a && b;}
uint16_t binop_logical_or(uint16_t a, uint16_t b) {return a || b;}
uint16_t binop_power(uint16_t x, uint16_t exponent)
{
    uint16_t result = 1;
    for (int i = 0; i < exponent; ++i)
        result *= x;
    return result;
}

typedef uint16_t (*FUNC_PTR)(uint16_t, uint16_t);

void binop(ds3_exe_result* exe, FUNC_PTR bin_func)
{
  uint16_t rhs, lhs;
  uint8_t op_result = stack_pop(&arithmetic_stack, &rhs);
  if(op_result != STACK_OP_OK)
  {
    exe->result = op_result;
    return;
  }
  op_result = stack_pop(&arithmetic_stack, &lhs);
  if(op_result != STACK_OP_OK)
  {
    exe->result = op_result;
    return;
  }
  op_result = stack_push(&arithmetic_stack, bin_func(lhs, rhs));
  if(op_result != STACK_OP_OK)
  {
    exe->result = op_result;
    return;
  }
}

#define VAR_BOUNDARY (0x1f)

void store_uint16_as_two_bytes_at(uint16_t addr, uint16_t value)
{
  var_buf[addr] = value & 0xff;
  var_buf[addr+1] = value >> 8;
}

void write_var(uint16_t addr, uint16_t value)
{
  if(addr == DEFAULTDELAY_ADDR)
    defaultdelay_value = value;
  else if (addr == DEFAULTCHARDELAY_ADDR)
    defaultchardelay_value = value;
  else if (addr == CHARJITTER_ADDR)
    charjitter_value = value;
  else if (addr == _RANDOM_MIN)
    rand_min = value;
  else if (addr == _RANDOM_MAX)
    rand_max = value;
  else if (addr == _RANDOM_INT)
    ; // this is read only, so do nothing
  else if (addr == _TIME_MS)
    ; // this is read only, so do nothing
  else if (addr == _TIME_S)
    ; // this is read only, so do nothing
  else if (addr == _READKEY)
    ; // this is read only, so do nothing
  else if (addr == _LOOP_SIZE)
    loop_size = value;
  else if (addr == _KEYPRESS_COUNT)
    ; // this is read only, so do nothing
  else if (addr == _NEEDS_EPILOGUE)
    epilogue_actions = value; // this is read only, so do nothing
  else if(addr < VAR_BUF_SIZE)
    store_uint16_as_two_bytes_at(addr, value);
}

uint8_t current_key;
uint16_t read_var(uint16_t addr)
{
  if(addr == DEFAULTDELAY_ADDR)
    return defaultdelay_value;
  else if (addr == DEFAULTCHARDELAY_ADDR)
    return defaultchardelay_value;
  else if (addr == CHARJITTER_ADDR)
    return charjitter_value;
  else if (addr == _RANDOM_MIN)
    return rand_min;
  else if (addr == _RANDOM_MAX)
    return rand_max;
  else if (addr == _RANDOM_INT)
    return (rand() + htim6.Instance->CNT) % (rand_max + 1 - rand_min) + rand_min;
  else if (addr == _TIME_MS)
    return (uint16_t)HAL_GetTick();
  else if (addr == _TIME_S)
    return (uint16_t)(HAL_GetTick() / 1000);
  else if (addr == _LOOP_SIZE)
    return loop_size;
  else if (addr == _READKEY)
    return get_first_active_key(current_key);
  else if (addr == _KEYPRESS_COUNT)
    return key_press_count[current_key];
  else if (addr == _NEEDS_EPILOGUE)
    return epilogue_actions;
  else if(addr < VAR_BUF_SIZE)
    return make_uint16(var_buf[addr], var_buf[addr+1]);
  return 0;
}

#define STR_BUF_SIZE 8
char make_str_buf[STR_BUF_SIZE];

char* make_str(uint16_t str_start_addr)
{
  uint16_t curr_addr = str_start_addr;
  uint8_t this_char, lsb, msb;
  memset(read_buffer, 0, READ_BUF_SIZE);
  while(1)
  {
    this_char = read_byte(curr_addr);
    if(this_char == 0)
      break;

    if(this_char == VAR_BOUNDARY)
    {
      curr_addr++;
      lsb = read_byte(curr_addr);
      curr_addr++;
      msb = read_byte(curr_addr);
      curr_addr++;
      curr_addr++;
      uint16_t var_addr = make_uint16(lsb, msb);
      uint16_t var_value = read_var(var_addr);
      memset(make_str_buf, 0, STR_BUF_SIZE);
      sprintf(make_str_buf, "%d", var_value);
      strcat(read_buffer, make_str_buf);
      continue;
    }
    memset(make_str_buf, 0, STR_BUF_SIZE);
    sprintf(make_str_buf, "%c", this_char);
    strcat(read_buffer, make_str_buf);
    curr_addr++;
  }
  return read_buffer;
  // kb_print(read_buffer, defaultchardelay_value, charjitter_value);
}

uint16_t index, red, green, blue;
void parse_color(uint8_t opcode, uint8_t keynum)
{
  stack_pop(&arithmetic_stack, &blue);
  stack_pop(&arithmetic_stack, &green);
  stack_pop(&arithmetic_stack, &red);
  stack_pop(&arithmetic_stack, &index);

  if(index == 0)
    index = keynum;
  else
    index--;
  if(index >= MAPPABLE_KEY_COUNT)
    return;
  set_pixel_3color_update_buffer(index, red, green, blue);
  neopixel_update();
}

void parse_swcf(void)
{
  stack_pop(&arithmetic_stack, &blue);
  stack_pop(&arithmetic_stack, &green);
  stack_pop(&arithmetic_stack, &red);
  for (int i = 0; i < NEOPIXEL_COUNT; ++i)
    set_pixel_3color_update_buffer(i, red, green, blue);
  neopixel_update();
}

void parse_swcr(uint8_t keynum)
{
  uint16_t swcr_arg;
  stack_pop(&arithmetic_stack, &swcr_arg);

  if(swcr_arg == 0)
    swcr_arg = keynum;
  else
    swcr_arg--;

  if(swcr_arg >= MAPPABLE_KEY_COUNT)
    redraw_bg();
  else
    key_reset(swcr_arg);
  osDelay(1);
}

void parse_olc(void)
{
  uint16_t xxx, yyy;
  stack_pop(&arithmetic_stack, &yyy);
  stack_pop(&arithmetic_stack, &xxx);
  if(xxx >= SSD1306_WIDTH || yyy >= SSD1306_HEIGHT)
    return;
  ssd1306_SetCursor(xxx, yyy);
}

void execute_instruction(uint16_t curr_pc, ds3_exe_result* exe, uint8_t keynum)
{
  uint8_t this_opcode = read_byte(curr_pc);
  uint8_t byte0 = read_byte(curr_pc+1);
  uint8_t byte1 = read_byte(curr_pc+2);
  uint8_t op_result;
  uint16_t op_data = make_uint16(byte0, byte1);
  current_key = keynum;
  // printf("PC: %04d | Opcode: %02d | 0x%02x 0x%02x | 0x%04x\n", curr_pc, this_opcode, byte0, byte1, op_data);
  
  exe->result = EXE_OK;
  exe->next_pc = curr_pc + INSTRUCTION_SIZE_BYTES;
  exe->data = 0;

  HAL_IWDG_Refresh(&hiwdg);

  if(this_opcode == OP_NOP)
  {
    return;
  }
  else if(this_opcode == OP_PUSHC)
  {
    op_result = stack_push(&arithmetic_stack, op_data);
    if(op_result != STACK_OP_OK)
    {
      exe->result = op_result;
      return;
    }
  }
  else if(this_opcode == OP_PUSHV)
  {
    op_result = stack_push(&arithmetic_stack, read_var(op_data));
    if(op_result != STACK_OP_OK)
    {
      exe->result = op_result;
      return;
    }
  }
  else if(this_opcode == OP_POP)
  {
    uint16_t this_item;
    op_result = stack_pop(&arithmetic_stack, &this_item);
    if(op_result != STACK_OP_OK)
    {
      exe->result = op_result;
      return;
    }
    write_var(op_data, this_item);
  }
  else if(this_opcode == OP_BRZ)
  {
    uint16_t this_value;
    op_result = stack_pop(&arithmetic_stack, &this_value);
    if(op_result != STACK_OP_OK)
    {
      exe->result = op_result;
      return;
    }
    if(this_value == 0)
      exe->next_pc = op_data;
  }
  else if(this_opcode == OP_JMP)
  {
    exe->next_pc = op_data;
  }
  else if(this_opcode == OP_CALL)
  {
    op_result = stack_push(&call_stack, exe->next_pc);
    if(op_result != STACK_OP_OK)
    {
      exe->result = op_result;
      return;
    }
    exe->next_pc = op_data;
  }
  else if(this_opcode == OP_RET)
  {
    uint16_t return_pc;
    op_result = stack_pop(&call_stack, &return_pc);
    if(op_result != STACK_OP_OK)
    {
      exe->result = op_result;
      return;
    }
    exe->next_pc = return_pc;
  }
  else if(this_opcode == OP_HALT)
  {
    exe->result = EXE_HALT;
  }
  else if(this_opcode == OP_EQ)
  {
    binop(exe, binop_equal);
  }
  else if(this_opcode == OP_NOTEQ)
  {
    binop(exe, binop_not_equal);
  }
  else if(this_opcode == OP_LT)
  {
    binop(exe, binop_lower);
  }
  else if(this_opcode == OP_LTE)
  {
    binop(exe, binop_lower_eq);
  }
  else if(this_opcode == OP_GT)
  {
    binop(exe, binop_greater);
  }
  else if(this_opcode == OP_GTE)
  {
    binop(exe, binop_greater_eq);
  }
  else if(this_opcode == OP_ADD)
  {
    binop(exe, binop_add);
  }
  else if(this_opcode == OP_SUB)
  {
    binop(exe, binop_sub);
  }
  else if(this_opcode == OP_MULT)
  {
    binop(exe, binop_mul);
  }
  else if(this_opcode == OP_DIV)
  {
    binop(exe, binop_divide);
  }
  else if(this_opcode == OP_MOD)
  {
    binop(exe, binop_mod);
  }
  else if(this_opcode == OP_POW)
  {
    binop(exe, binop_power);
  }
  else if(this_opcode == OP_LSHIFT)
  {
    binop(exe, binop_lshift);
  }
  else if(this_opcode == OP_RSHIFT)
  {
    binop(exe, binop_rshift);
  }
  else if(this_opcode == OP_BITOR)
  {
    binop(exe, binop_bitwise_or);
  }
  else if(this_opcode == OP_BITAND)
  {
    binop(exe, binop_bitwise_and);
  }
  else if(this_opcode == OP_LOGIOR)
  {
    binop(exe, binop_logical_or);
  }
  else if(this_opcode == OP_LOGIAND)
  {
    binop(exe, binop_logical_and);
  }
  else if(this_opcode == OP_STR || this_opcode == OP_STRLN)
  {
    char* str_buf = make_str(op_data);
    kb_print(str_buf, defaultchardelay_value, charjitter_value);
    if(this_opcode == OP_STRLN)
    {
    	press_key(0x28, 0x03); // ENTER key
    	osDelay(defaultdelay_value);
    	release_key(0x28, 0x03);
    	osDelay(defaultdelay_value);
    }
  }
  else if(this_opcode == OP_EMUK)
  {
    exe->data = byte0;
    exe->data2 = byte1;
    exe->result = EXE_ACTION_EMUK;
  }
  else if(this_opcode == OP_KDOWN)
  {
  	press_key(byte0, byte1);
  	osDelay(defaultdelay_value);
  }
  else if(this_opcode == OP_KUP)
  {
  	release_key(byte0, byte1);
  	osDelay(defaultdelay_value);
  }
  else if(this_opcode == OP_MMOV)
  {
    my_key kk;
    kk.code = byte1;
    kk.code2 = byte0;
    kk.type = KEY_TYPE_MOUSE_MOVEMENT;
    keyboard_press(&kk, 0);
    osDelay(defaultdelay_value);
  }
  else if(this_opcode == OP_DELAY)
  {
    uint16_t delay_amount;
    op_result = stack_pop(&arithmetic_stack, &delay_amount);
    if(op_result != STACK_OP_OK)
    {
      exe->result = op_result;
      return;
    }
    osDelay(delay_amount);
  }
  else if(this_opcode == OP_MSCL)
  {
    my_key kk;
    kk.code = byte0;
    kk.code2 = 0;
    kk.type = KEY_TYPE_MOUSE_WHEEL;
    keyboard_press(&kk, 0);
    osDelay(defaultchardelay_value);
    keyboard_release(&kk);
    osDelay(defaultdelay_value);
  }
  else if(this_opcode == OP_SWCC)
  {
    parse_color(this_opcode, keynum);
  }
  else if(this_opcode == OP_SWCF)
  {
    parse_swcf();
  }
  else if(this_opcode == OP_SWCR)
  {
    parse_swcr(keynum);
  }
  else if(this_opcode == OP_OLC)
  {
    parse_olc();
  }
  else if(this_opcode == OP_OLP)
  {
    char* str_buf = make_str(op_data);
    ssd1306_WriteString(str_buf, Font_6x10,White);
  }
  else if(this_opcode == OP_OLU)
  {
    ssd1306_UpdateScreen();
  }
  else if(this_opcode == OP_OLB)
  {
    ssd1306_Fill(Black);
  }
  else if(this_opcode == OP_OLR)
  {
    print_legend();
  }
  else if(this_opcode == OP_BCLR)
  {
    button_service_all();
  }
  else if(this_opcode == OP_NEXTP)
  {
    exe->result = EXE_ACTION_NEXT_PROFILE;
  }
  else if(this_opcode == OP_PREVP)
  {
    exe->result = EXE_ACTION_PREV_PROFILE;
  }
  else if(this_opcode == OP_SLEEP)
  {
    exe->result = EXE_ACTION_SLEEP;
  }
  else if(this_opcode == OP_GOTOP)
  {
    uint16_t target_profile;
    op_result = stack_pop(&arithmetic_stack, &target_profile);
    if(op_result != STACK_OP_OK)
    {
      exe->result = op_result;
      return;
    }
    exe->result = EXE_ACTION_GOTO_PROFILE;
    exe->data = (uint8_t)target_profile;
  }
  else
  {
    // UNKNOWN OP CODE
    exe->result = EXE_ERROR;
  }
}

uint8_t switch_bank(uint16_t addr)
{
  uint8_t target_bank = addr/BIN_BUF_SIZE;
  if(target_bank == current_bank)
    return DSB_OK;

  // printf("\n---cc:%d, tc:%d---\n", current_bank, target_bank);
  uint8_t op_result = DSB_OK;
  UINT bytes_read = 0;
  if(f_open(&sd_file, temp_buf, FA_READ) != 0)
  {
    op_result = DSB_FOPEN_FAILED;
    goto switch_bank_end;
  }

  if(addr >= f_size(&sd_file))
  {
    op_result = DSB_READ_OVERFLOW;
    goto switch_bank_end;
  }

  if(f_lseek(&sd_file, target_bank*BIN_BUF_SIZE) != 0)
  {
    op_result = DSB_CHUNK_LOAD_ERROR;
    goto switch_bank_end;
  }

  memset(bin_buf, 0, BIN_BUF_SIZE);
  f_read(&sd_file, bin_buf, BIN_BUF_SIZE, &bytes_read);
  current_bank = target_bank;
  switch_bank_end:
  f_close(&sd_file);
  return op_result;
}

uint8_t read_byte(uint16_t addr)
{
  taskENTER_CRITICAL();
  uint8_t bank_switch_result = switch_bank(addr);
  taskEXIT_CRITICAL();
  if(bank_switch_result != DSB_OK)
  {
    keyboard_release_all();
    error_animation(0);
    osDelay(2000);
    NVIC_SystemReset();
  }
  return bin_buf[addr%BIN_BUF_SIZE];
}

void run_dsb(ds3_exe_result* er, uint8_t keynum)
{
  uint16_t current_pc = 0;
	current_bank = 255;
  stack_init(&arithmetic_stack);
  stack_init(&call_stack);
  defaultdelay_value = DEFAULT_CMD_DELAY_MS;
  defaultchardelay_value = DEFAULT_CHAR_DELAY_MS;
  charjitter_value = 0;
  rand_max = 65535;
  rand_min = 0;
  loop_size = 0;
  epilogue_actions = 0;
  srand(HAL_GetTick());

  while(1)
  {
    execute_instruction(current_pc, er, keynum);
    if(er->result != EXE_OK)
      break;
    current_pc = er->next_pc;
  }
  er->epilogue_actions = epilogue_actions;
  // printf("execution halted: %d\n", er->result);
}
