dekuNukem/duckyPad/firmware/evo/Inc/profiles.h

#ifndef __PROFILES_H
#define __PROFILES_H

#ifdef __cplusplus
 extern "C" {
#endif

#include <stdint.h>

#include "input_task.h"
#include "neopixel.h"
#include "fatfs.h"

#define FILENAME_BUFSIZE 48
#define MAX_PROFILES 32
#define KEYNAME_SIZE 8
#define PROFILE_NAME_MAX_LEN 16

typedef struct
{
  uint8_t brightness_index;
  uint8_t sleep_index;
  uint8_t last_used_profile;
  char current_kb_layout[FILENAME_BUFSIZE];
} dp_global_settings;

typedef struct
{
  char sw_name[MECH_OBSW_COUNT][KEYNAME_SIZE];
  uint8_t sw_color_default[MECH_OBSW_COUNT][THREE]; // only mechanical keys have RGB LEDs
  uint8_t sw_color_user_assigned[MECH_OBSW_COUNT][THREE];
  uint8_t sw_color_keydown[MECH_OBSW_COUNT][THREE];
  uint8_t keypress_count[MAX_TOTAL_SW_COUNT];
  uint8_t has_user_assigned_keycolor[MECH_OBSW_COUNT];
  // f_stat() is super slow (30ms)
  // Bit 0 (LSB): on_press exist, bit 1: on_release exist
  uint8_t dsb_exists[MAX_TOTAL_SW_COUNT];
  uint8_t dim_unused_keys;
} profile_cache;

#define DSB_ON_PRESS_EXISTS 0x1
#define DSB_ON_RELEASE_EXISTS 0x2

extern profile_cache curr_pf_info;

extern dp_global_settings dp_settings;
extern uint8_t current_profile_number;
extern char profile_name_list[MAX_PROFILES][PROFILE_NAME_MAX_LEN];

uint8_t mount_sd(void);
uint8_t scan_profiles(void);
uint8_t load_profile(uint8_t profile_number);
void goto_profile(uint8_t profile_number);
void goto_prev_profile(void);
void goto_next_profile(void);

uint8_t load_settings(dp_global_settings* dps);
uint8_t save_settings(dp_global_settings* dps);
void save_persistent_state(void);
uint8_t load_persistent_state(void);
void save_gv(void);
void load_gv(void);
uint8_t load_keymap_by_name(char* km_name);
uint8_t get_next_keymap(const char* current_keymap_filename, char* next_keymap_filename);
uint8_t get_first_keymap(char* keymap_filename);
uint8_t goto_profile_without_updating_rgb_LED(uint8_t profile_number);
void profile_init(void);

uint8_t ensure_new_profile_format(void);

#define PROFILE_SCAN_OK 0
#define PROFILE_SCAN_ERROR_NO_TOC 1
#define PROFILE_SCAN_ERROR_NO_PROFILE 2

#define ERROR_NO_KEYMAP_FOLDER 1
#define ERROR_KEYMAP_NOT_FOUND 2

extern FRESULT sd_fresult;
extern FATFS sd_fs;
extern FIL sd_file;
extern DIR dir;
extern FILINFO fno;
extern UINT bytes_written, bytes_read;

extern char lfn_buf[FILENAME_BUFSIZE];

#ifdef __cplusplus
}
#endif

#endif
