dekuNukem/duckyPad/firmware/evo/Inc/md5.h

#ifndef MD5_H
#define MD5_H

#include <stdio.h>
#include <stdint.h>
#include <string.h>
#include <stdlib.h>
#include "fatfs.h"

typedef struct{
    uint64_t size;        // Size of input in bytes
    uint32_t buffer[4];   // Current accumulation of hash
    uint8_t input[64];    // Input to be used in the next step
    uint8_t digest[16];   // Result of algorithm
}MD5Context;

void md5Init(MD5Context *ctx);
void md5Update(MD5Context *ctx, uint8_t *input, size_t input_len);
void md5Finalize(MD5Context *ctx);
void md5Step(uint32_t *buffer, uint32_t *input);

void md5String(char *input, uint8_t *result);
uint8_t md5File(FIL* source_file, uint8_t *result);

void print_hash(uint8_t *p);

#define MD5_BUF_SIZE 16

#endif
