dekuNukem/duckyPad/firmware/code/Inc/ds3_vm.h

#include "stm32f0xx_hal.h"

#ifndef ds3_vm_h
#define ds3_vm_h

#define OP_NOP 0
#define OP_PUSHC 1
#define OP_PUSHV 2
#define OP_POP 3
#define OP_BRZ 4
#define OP_JMP 5
#define OP_CALL 6
#define OP_RET 7
#define OP_HALT 8
#define OP_EQ 9
#define OP_NOTEQ 10
#define OP_LT 11
#define OP_LTE 12
#define OP_GT 13
#define OP_GTE 14
#define OP_ADD 15
#define OP_SUB 16
#define OP_MULT 17
#define OP_DIV 18
#define OP_MOD 19
#define OP_POW 20
#define OP_LSHIFT 21
#define OP_RSHIFT 22
#define OP_BITOR 23
#define OP_BITAND 24
#define OP_LOGIAND 25
#define OP_LOGIOR 26
#define OP_DELAY 27
#define OP_KUP 28
#define OP_KDOWN 29
#define OP_MSCL 30
#define OP_MMOV 31
#define OP_SWCF 32
#define OP_SWCC 33
#define OP_SWCR 34
#define OP_STR 35
#define OP_STRLN 36
#define OP_EMUK 37
#define OP_OLC 38
#define OP_OLP 39
#define OP_OLU 40
#define OP_OLB 41
#define OP_OLR 42
#define OP_BCLR 43
#define OP_PREVP 44
#define OP_NEXTP 45
#define OP_GOTOP 46
#define OP_SLEEP 47

#define INSTRUCTION_SIZE_BYTES 3
#define STACK_SIZE 8

#define EXE_OK 0

#define EXE_ACTION_SLEEP 1
#define EXE_ACTION_PREV_PROFILE 2
#define EXE_ACTION_NEXT_PROFILE 3
#define EXE_ACTION_GOTO_PROFILE 4
#define EXE_ACTION_EMUK 5

#define EXE_HALT 20
#define EXE_EMPTY_FILE 21
#define EXE_ERROR 30

#define DSB_OK 0
#define DSB_FOPEN_FAILED 50
#define DSB_FREAD_ERROR 60
#define DSB_CHUNK_LOAD_ERROR 70
#define DSB_READ_OVERFLOW 80

#define STACK_OP_OK 0
#define STACK_OP_OVERFLOW 100
#define STACK_OP_UNDERFLOW 110

#define DEFAULTDELAY_ADDR (0xffff - 0)
#define DEFAULTCHARDELAY_ADDR (0xffff - 1)
#define CHARJITTER_ADDR (0xffff - 2)
#define _RANDOM_MIN (0xffff - 3)
#define _RANDOM_MAX (0xffff - 4)
#define _RANDOM_INT (0xffff - 5)
#define _TIME_MS (0xffff - 6)
#define _READKEY (0xffff - 7)
#define _LOOP_SIZE (0xffff - 8)
#define _KEYPRESS_COUNT (0xffff - 9)
#define _NEEDS_EPILOGUE  (0xffff - 10)
#define _TIME_S  (0xffff - 11)

typedef struct
{
  uint8_t result;
  uint16_t next_pc;
  uint8_t data;
  uint8_t data2;
  uint8_t epilogue_actions;
} ds3_exe_result;

uint8_t load_dsb(char* filename);
void run_dsb(ds3_exe_result* er, uint8_t keynum);
void release_key(uint8_t code, uint8_t type);
uint8_t read_byte(uint16_t addr);
uint8_t write_byte(uint16_t addr, uint8_t data);

#endif
