dekuNukem/duckyPad/firmware/code/Inc/buttons.h

#ifndef __BUTTONS_H
#define __BUTTONS_H

#ifdef __cplusplus
 extern "C" {
#endif 

#include "stm32f0xx_hal.h"

#define KEY_COUNT 17
#define MAPPABLE_KEY_COUNT 15
#define KEY_0 0
#define KEY_1 1
#define KEY_2 2
#define KEY_3 3
#define KEY_4 4
#define KEY_5 5
#define KEY_6 6
#define KEY_7 7
#define KEY_8 8
#define KEY_9 9
#define KEY_10 10
#define KEY_11 11
#define KEY_12 12
#define KEY_13 13
#define KEY_14 14
#define KEY_BUTTON1 15
#define KEY_BUTTON2 16
#define BUTTON_SERVICE_UNSERVICED 0
#define BUTTON_SERVICE_SERVICED 1
#define BUTTON_RELEASED 0   
#define BUTTON_PRESSED 1

typedef struct
{
  uint8_t prev_state;
  uint8_t button_state;
  uint8_t service_status; 
} but_status;

extern but_status button_status[KEY_COUNT];

uint8_t is_pressed(uint8_t which);
void service_press(uint8_t which);
void keyboard_update(void);
uint8_t is_released_but_not_serviced(uint8_t which);
uint8_t get_first_active_key(uint8_t curr_key);
void button_service_all(void);
uint8_t is_released(uint8_t which);
#ifdef __cplusplus
}
#endif

#endif
