dekuNukem/duckyPad/resources/profile_generator/duck_test/profile11_fact/config.txt

z1 poem
z2 income
z3 girlfri
z4 revolut
z5 news
z6 operati
z7 freedom
z8 teachin
z9 paintin
z10 quantit
z11 history
z12 percent
z13 sample
z14 traditi
z15 history
SWCOLOR_1 64 8 16 
SWCOLOR_2 16 16 32 
SWCOLOR_3 32 64 8 
SWCOLOR_4 8 16 8 
SWCOLOR_5 64 32 16 
SWCOLOR_6 16 64 16 
SWCOLOR_7 16 64 16 
SWCOLOR_8 64 64 8 
SWCOLOR_9 16 32 32 
SWCOLOR_10 16 8 32 
SWCOLOR_11 16 16 32 
SWCOLOR_12 64 16 32 
SWCOLOR_13 64 64 16 
SWCOLOR_14 16 64 16 
SWCOLOR_15 64 16 16 
