dekuNukem/duckyPad/resources/profile_generator/duck_test/profile12_painting/config.txt

z1 coffee
z2 sympath
z3 garbage
z4 resolut
z5 departu
z6 context
z7 selecti
z8 champio
z9 sample
z10 apple
z11 cookie
z12 quantit
z13 sample
z14 platfor
z15 nation
SWCOLOR_1 32 32 16 
SWCOLOR_2 16 64 16 
SWCOLOR_3 64 64 32 
SWCOLOR_4 32 8 16 
SWCOLOR_5 32 32 32 
SWCOLOR_6 64 32 32 
SWCOLOR_7 16 8 8 
SWCOLOR_8 64 32 16 
SWCOLOR_9 64 8 8 
SWCOLOR_10 8 16 16 
SWCOLOR_11 8 32 32 
SWCOLOR_12 32 8 8 
SWCOLOR_13 16 16 16 
SWCOLOR_14 16 64 16 
SWCOLOR_15 32 32 64 
