dekuNukem/duckyPad/resources/profile_generator/duck_test/profile14_nation/config.txt

z1 meaning
z2 winner
z3 strateg
z4 apartme
z5 equipme
z6 power
z7 apartme
z8 income
z9 drama
z10 girlfri
z11 pizza
z12 editor
z13 setting
z14 knowled
z15 editor
SWCOLOR_1 32 8 32 
SWCOLOR_2 8 64 64 
SWCOLOR_3 16 16 64 
SWCOLOR_4 64 8 8 
SWCOLOR_5 8 64 64 
SWCOLOR_6 64 64 8 
SWCOLOR_7 8 64 64 
SWCOLOR_8 32 32 8 
SWCOLOR_9 8 16 64 
SWCOLOR_10 32 32 32 
SWCOLOR_11 8 64 16 
SWCOLOR_12 32 8 64 
SWCOLOR_13 32 32 32 
SWCOLOR_14 32 16 64 
SWCOLOR_15 16 64 16 
