dekuNukem/duckyPad/resources/profile_generator/duck_test/profile19_history/config.txt

z1 driver
z2 coffee
z3 literat
z4 ambitio
z5 growth
z6 cell
z7 river
z8 variati
z9 heart
z10 army
z11 mood
z12 map
z13 drawer
z14 instruc
z15 cancer
SWCOLOR_1 16 64 16 
SWCOLOR_2 8 16 64 
SWCOLOR_3 32 8 32 
SWCOLOR_4 64 32 32 
SWCOLOR_5 8 16 8 
SWCOLOR_6 8 8 32 
SWCOLOR_7 64 8 8 
SWCOLOR_8 64 32 32 
SWCOLOR_9 32 16 16 
SWCOLOR_10 64 8 8 
SWCOLOR_11 16 32 8 
SWCOLOR_12 32 32 32 
SWCOLOR_13 8 32 32 
SWCOLOR_14 8 32 64 
SWCOLOR_15 16 64 16 
