dekuNukem/duckyPad/resources/profile_generator/duck_test/profile20_literature/config.txt

z1 ratio
z2 sympath
z3 charity
z4 poetry
z5 way
z6 replace
z7 effort
z8 lake
z9 perform
z10 sample
z11 year
z12 polluti
z13 setting
z14 girlfri
z15 funeral
SWCOLOR_1 16 16 16 
SWCOLOR_2 64 32 64 
SWCOLOR_3 64 8 32 
SWCOLOR_4 16 32 8 
SWCOLOR_5 16 8 8 
SWCOLOR_6 32 16 64 
SWCOLOR_7 16 64 64 
SWCOLOR_8 64 64 64 
SWCOLOR_9 16 32 8 
SWCOLOR_10 16 32 64 
SWCOLOR_11 64 8 32 
SWCOLOR_12 64 16 8 
SWCOLOR_13 16 16 64 
SWCOLOR_14 16 16 32 
SWCOLOR_15 32 8 8 
