dekuNukem/duckyPad/resources/profile_generator/duck_test/profile22_nation/config.txt

z1 prefere
z2 traditi
z3 cousin
z4 champio
z5 televis
z6 tooth
z7 softwar
z8 grandmo
z9 apartme
z10 driver
z11 protect
z12 growth
z13 way
z14 law
z15 injury
SWCOLOR_1 16 32 8 
SWCOLOR_2 8 16 64 
SWCOLOR_3 64 16 16 
SWCOLOR_4 32 16 32 
SWCOLOR_5 16 8 16 
SWCOLOR_6 8 64 32 
SWCOLOR_7 16 32 32 
SWCOLOR_8 16 64 32 
SWCOLOR_9 16 32 64 
SWCOLOR_10 64 64 32 
SWCOLOR_11 16 64 16 
SWCOLOR_12 8 8 16 
SWCOLOR_13 32 8 16 
SWCOLOR_14 16 16 32 
SWCOLOR_15 16 8 8 
