dekuNukem/duckyPad/resources/profile_generator/duck_test/profile30_library/config.txt

z1 finding
z2 history
z3 child
z4 policy
z5 paper
z6 two
z7 drama
z8 map
z9 power
z10 library
z11 alcohol
z12 explana
z13 cousin
z14 paper
z15 chemist
SWCOLOR_1 8 64 16 
SWCOLOR_2 64 32 8 
SWCOLOR_3 8 8 64 
SWCOLOR_4 64 64 32 
SWCOLOR_5 32 8 64 
SWCOLOR_6 8 8 32 
SWCOLOR_7 16 16 8 
SWCOLOR_8 64 16 32 
SWCOLOR_9 16 16 64 
SWCOLOR_10 64 32 32 
SWCOLOR_11 8 64 64 
SWCOLOR_12 32 32 32 
SWCOLOR_13 32 8 16 
SWCOLOR_14 32 8 16 
SWCOLOR_15 32 16 32 
