dekuNukem/duckyPad/resources/profile_generator/duck_test/profile38_disaster/config.txt

z1 elevato
z2 estate
z3 penalty
z4 exam
z5 footbal
z6 power
z7 client
z8 people
z9 fact
z10 world
z11 leader
z12 nation
z13 law
z14 climate
z15 operati
SWCOLOR_1 8 8 32 
SWCOLOR_2 64 8 16 
SWCOLOR_3 16 64 32 
SWCOLOR_4 16 16 64 
SWCOLOR_5 64 8 32 
SWCOLOR_6 64 32 8 
SWCOLOR_7 16 32 32 
SWCOLOR_8 64 8 16 
SWCOLOR_9 64 32 64 
SWCOLOR_10 16 16 16 
SWCOLOR_11 64 8 32 
SWCOLOR_12 16 64 16 
SWCOLOR_13 8 8 32 
SWCOLOR_14 64 32 64 
SWCOLOR_15 64 64 64 
