dekuNukem/duckyPad/resources/profile_generator/duck_test/profile3_power/config.txt

z1 charity
z2 proposa
z3 army
z4 apartme
z5 mood
z6 cookie
z7 strateg
z8 power
z9 televis
z10 percept
z11 editor
z12 introdu
z13 poetry
z14 boyfrie
z15 tea
SWCOLOR_1 8 64 64 
SWCOLOR_2 64 16 16 
SWCOLOR_3 64 16 32 
SWCOLOR_4 32 16 32 
SWCOLOR_5 16 64 32 
SWCOLOR_6 32 32 64 
SWCOLOR_7 16 32 32 
SWCOLOR_8 16 32 16 
SWCOLOR_9 64 64 32 
SWCOLOR_10 8 32 16 
SWCOLOR_11 16 8 32 
SWCOLOR_12 8 64 8 
SWCOLOR_13 16 32 32 
SWCOLOR_14 8 16 16 
SWCOLOR_15 16 64 16 
