dekuNukem/duckyPad/resources/profile_generator/duck_test/profile43_coffee/config.txt

z1 gate
z2 driver
z3 recogni
z4 union
z5 leader
z6 writing
z7 protect
z8 committ
z9 gate
z10 power
z11 meaning
z12 law
z13 law
z14 assumpt
z15 insuran
SWCOLOR_1 16 16 64 
SWCOLOR_2 64 64 32 
SWCOLOR_3 16 8 64 
SWCOLOR_4 64 64 16 
SWCOLOR_5 32 64 64 
SWCOLOR_6 32 8 8 
SWCOLOR_7 32 64 64 
SWCOLOR_8 64 8 16 
SWCOLOR_9 64 8 64 
SWCOLOR_10 64 8 32 
SWCOLOR_11 32 32 32 
SWCOLOR_12 16 64 8 
SWCOLOR_13 64 32 64 
SWCOLOR_14 8 64 64 
SWCOLOR_15 64 16 8 
