dekuNukem/duckyPad/resources/profile_generator/duck_test/profile44_union/config.txt

z1 meaning
z2 elevato
z3 food
z4 player
z5 country
z6 writing
z7 explana
z8 driver
z9 message
z10 charity
z11 income
z12 organiz
z13 poetry
z14 history
z15 recogni
SWCOLOR_1 64 64 64 
SWCOLOR_2 8 32 8 
SWCOLOR_3 16 16 16 
SWCOLOR_4 16 64 64 
SWCOLOR_5 16 64 8 
SWCOLOR_6 16 32 32 
SWCOLOR_7 8 64 16 
SWCOLOR_8 32 64 16 
SWCOLOR_9 64 8 16 
SWCOLOR_10 64 8 64 
SWCOLOR_11 16 32 16 
SWCOLOR_12 16 8 32 
SWCOLOR_13 64 32 64 
SWCOLOR_14 8 32 64 
SWCOLOR_15 64 32 32 
