dekuNukem/duckyPad/resources/profile_generator/duck_test/profile47_bonus/config.txt

z1 variati
z2 foundat
z3 church
z4 funeral
z5 office
z6 world
z7 power
z8 ambitio
z9 poet
z10 poetry
z11 securit
z12 footbal
z13 policy
z14 drama
z15 traditi
SWCOLOR_1 16 64 32 
SWCOLOR_2 32 64 8 
SWCOLOR_3 16 64 8 
SWCOLOR_4 16 32 64 
SWCOLOR_5 64 64 8 
SWCOLOR_6 64 64 16 
SWCOLOR_7 16 64 8 
SWCOLOR_8 16 8 64 
SWCOLOR_9 16 16 16 
SWCOLOR_10 8 32 8 
SWCOLOR_11 16 8 8 
SWCOLOR_12 16 16 8 
SWCOLOR_13 8 8 8 
SWCOLOR_14 8 16 8 
SWCOLOR_15 16 8 64 
