dekuNukem/duckyPad/sample_profiles/profile7_eagleEDA/config.txt

z1 esc
z2 ratnest
z3 ripall
z4 route
z5 ripup
z6 copy
z7 move
z8 delete
z9 name
z10 value
z11 net
z12 label
z13 add
z14 info
z15 group
BG_COLOR 128 0 64
SWCOLOR_1 255 0 0
SWCOLOR_2 255 95 0
SWCOLOR_3 255 191 0
SWCOLOR_4 223 255 0
SWCOLOR_5 127 255 0
SWCOLOR_6 31 255 0
SWCOLOR_7 0 255 63
SWCOLOR_8 0 255 159
SWCOLOR_9 0 255 255
SWCOLOR_10 0 159 255
SWCOLOR_11 0 63 255
SWCOLOR_12 31 0 255
SWCOLOR_13 127 0 255
SWCOLOR_14 223 0 255
SWCOLOR_15 255 0 191
